QuickRecon/DiveCANHead/Firmware/BENCHTEST.md

# DiveCAN Jr Hardware-in-the-Loop Test Checklist

Manual hardware bench tests required before merging changes to the
OTA, power, or boot subsystems. Each entry is structured so it can be
lifted into the `tests/integration/` pytest harness later —
preconditions, actions, and pass criteria are expressed in concrete,
scriptable terms.

The existing integration harness (Arduino Due cell-shim, Riden PSU
control, CAN dongle) supplies most of the plumbing needed to automate
each entry. Until that automation exists, these are run by hand
during phase merges and the results recorded in the PR description.

**Maintenance directive:** when adding or modifying a safety-critical
behaviour, add or update the corresponding entry here in the same PR.
Same convention as `ARCHITECTURE.md` and `COMPROMISE.md`.

---

## Section 1 — Boot & power (Phase 1)

### BT-1.1 Cold-boot from clean flash

- **Pre:** Unit freshly programmed via `flash.sh` (MCUBoot + signed
  app via sysbuild merged hex). External NOR fully erased
  (`flash_erase 0 64M` on the SPI NOR via probe).
- **Action:** Power on. Observe heartbeat LED and RTT log.
- **Pass:**
  - MCUBoot startup messages on RTT within 1 s.
  - Heartbeat LED blinks during MCUBoot's pre-boot window
    (driven by `CONFIG_MCUBOOT_INDICATION_LED`).
  - App reaches its main loop within 3 s of power-on.
  - App's heartbeat thread takes over the LED.
  - No errors in MCUBoot output relating to slot1/scratch
    (acceptable: "no image in secondary slot" — slot is empty).

### BT-1.2 Settings persistence across reboot

- **Pre:** BT-1.1 passed. Unit is running normally.
- **Action:**
  1. Write a known runtime setting via UDS (e.g. PPO2 control mode
     to a non-default value).
  2. Power-cycle.
  3. Read the setting back via UDS.
- **Pass:** The setting matches what was written. Confirms NVS
  storage on external NOR is functional.

### BT-1.3 Mid-erase power pull on external NOR

- **Pre:** Begin a `flash_erase` operation on the slot1 partition
  (192–224 KB region). Pull power at ~50 % of the erase.
- **Action:** Restore power. Observe boot.
- **Pass:**
  - Unit boots from slot0 (running app).
  - No MCUBoot stall — partial-erased slot1 may report "no image"
    or "invalid header" in RTT, both acceptable.
  - App reaches main loop.
  - No persistent fault state in error histogram (0xF260).

### BT-1.4 IWDG survival across MCUBoot startup

- **Pre:** Soft-reset the unit via `sys_reboot()` (e.g. from a UDS
  command in a confirmed image).
- **Action:** Observe boot.
- **Pass:**
  - IWDG (8 s window) does NOT trip during MCUBoot's hash walk +
    swap-state read.
  - App reaches its main loop within the same ~3 s budget as
    BT-1.1.
  - Implicit confirmation of `CONFIG_BOOT_WATCHDOG_FEED=y` working.

### BT-1.5 Heartbeat-LED handoff

- **Pre:** Unit running normally for ≥30 s.
- **Action:** Visually inspect heartbeat LED behaviour across a
  power cycle.
- **Pass:**
  - During MCUBoot window: LED blinks at MCUBoot's
    indication-LED cadence (typically faster than the app's
    heartbeat).
  - After app boot: LED blinks at the app's heartbeat cadence.
  - Smooth handoff, no extended dark period.

### BT-1.6 Signed slot0 image validates on every boot (Phase 2)

- **Pre:** Unit programmed via `flash.sh` (sysbuild merged hex
  containing MCUBoot + an imgtool-signed v0.0.0+0 app). MCUBoot
  Kconfig has `CONFIG_BOOT_VALIDATE_SLOT0=y` (verify via
  `grep BOOT_VALIDATE build/mcuboot/zephyr/.config`).
- **Action:** Cold power-cycle and observe RTT log up to the app
  banner.
- **Pass:**
  - MCUBoot logs a successful slot0 validation pass (no
    `Image in the primary slot is not valid!` line).
  - App banner `DiveCAN Jr — Zephyr <version>` appears.
  - SHA-256 walk completes in well under the 8 s IWDG window —
    confirms `BOOT_WATCHDOG_FEED=y` is alive during the hash.
- **Notes:** Image layout reference (from `scripts/sign_app.py`
  output): 512 B header + body + 40 B TLV (single SHA-256 entry,
  TLV type 0x10). `python3 imgtool.py verify` against the
  signed bin should print `Image was correctly validated`.

### BT-1.7 Corrupt byte in slot0 → MCUBoot refuses to jump (Phase 2)

- **Pre:** Unit running normally from a known-good signed image.
  External NOR / slot1 state irrelevant.
- **Action:** Run `scripts/test_mcuboot_reject.sh`. The script:
  1. Copies the freshly-built `zephyr.signed.bin`, flips one byte
     at offset 0x1000 (past the 512 B header, before the TLV).
  2. Reflashes only slot0 at `0x08010000` via STM32CubeProgrammer —
     MCUBoot itself is untouched.
  3. Halts the chip via openocd, reads PC, dumps the SEGGER RTT
     up-buffer in RAM (`pBuffer`, `WrOff` from the control block).
  4. Prints the captured MCUBoot log + PASS/FAIL verdict.
- **Pass:**
  - Script prints **`PASS: MCUBoot rejected the corrupt image`**.
  - PC at halt is inside MCUBoot text (`< 0x08010000`).
  - When MCUBoot reaches its FIH_PANIC log path, the RTT buffer
    contains the textbook chain:
    `Image in the primary slot is not valid!` → `Unable to find
    bootable image`. (On the early-validation path the chip
    panics through `arch_system_halt` before that log line gets
    a chance — the PC check is still the authoritative verdict.)
  - Heartbeat LED does **not** transition to the app's cadence.
- **Recovery:** `./flash.sh` (the script prints this on exit too).
- **Notes:**
  - We dump the RTT up-buffer directly from RAM via openocd's
    `mdb` rather than running the live `rtt server` bridge.
    MCUBoot's writes happen in tens of ms during early boot and
    are long over by the time openocd's RTT poll thread finds
    the control block. The buffer-dump method is deterministic
    and avoids the host-attach race.
  - This is the most important defensive property of the
    bootloader and must remain green after any MCUBoot config
    change.
  - The pre-existing `E: Watchdog install timeout failed: -22`
    line in MCUBoot's output is unrelated — it fires whenever
    the L4 IWDG is already running from a prior boot, which is
    expected on warm-reset and harmless here (`BOOT_WATCHDOG_FEED`
    keeps the running IWDG fed regardless).

---

## Section 2 — OTA transfer (Phase 3)

The wire-protocol behaviour for SIDs 0x10 / 0x34 / 0x36 / 0x37 / 0x31 is
covered automatically by:

- **`tests/uds_ota/`** — native_sim ztest suite, 25 cases (run with
  `scripts/native_test.py run uds_ota`)
- **`tests/integration/harness/test_uds_ota.py`** — pytest E2E suite,
  8 cases over vcan against the real Zephyr firmware (run with
  `pytest test_uds_ota.py` from the harness venv)

The bench tests below catch what the host harness can't: the real
MCUBoot bootloader doing the actual swap on STM32L4 silicon. Until the
"Enable MCUBoot E2E on native_sim" follow-up lands, this section is the
authoritative coverage for the swap path.

### BT-2.1 Happy path: streamed image swaps in

- **Pre:** Unit running a confirmed v1 image. SD card / external NOR in
  whatever state — slot1 contents irrelevant.
- **Action:**
  1. Use the existing `tests/integration/harness/uds_ota.py` helpers (or
     equivalent dive-computer tool) over a USB CAN adapter:
     ```
     ota.enter_programming()
     ota.request_download(len(image))
     ota.transfer_image(image)
     ota.request_transfer_exit()
     ota.routine_activate()
     ```
  2. Wait ~15 s for MCUBoot's swap-using-scratch to complete.
  3. Power-cycle (or watch the reboot fire from the activate response).
- **Pass:**
  - Each UDS request gets a positive response (0x50 / 0x74 / 0x76 / 0x77
    / 0x71).
  - On the next boot, the running firmware is v2 (query DID 0xF000 to
    confirm).
  - No `Image in the primary slot is not valid!` line in MCUBoot's RTT
    log.
  - **The unit is now booting from a test-mode image — Phase 4 POST
    confirmation hasn't landed yet, so the image will revert on the
    next reboot unless `boot_write_img_confirmed()` is called manually
    via SWD.** This is the documented Phase 3 → Phase 4 gap; flagged in
    the OTA plan.

### BT-2.2 Header rejection at 0x37

- **Pre:** Unit running a confirmed image.
- **Action:** Run `tests/integration/harness/test_uds_ota.py`'s
  `truncate_image_header()` helper to zero the MCUBoot magic, then
  stream that corrupted image via 0x34 / 0x36 / 0x37.
- **Pass:**
  - 0x37 returns NRC (0x22 or 0x72).
  - slot0 is **untouched** — `mcuboot_swap_type()` reports
    BOOT_SWAP_TYPE_NONE on next read.
  - `boot_request_upgrade` was never called.

### BT-2.3 Hash rejection at 0x31 activate

- **Pre:** Unit running a confirmed image.
- **Action:** Use `corrupt_signed_image()` to flip a byte inside the
  body of a valid signed image. Stream the full 0x34/0x36/0x37/0x31
  sequence.
- **Pass:**
  - 0x37 succeeds (header magic + size still valid).
  - 0x31 returns NRC 0x22 (CONDITIONS_NOT_CORRECT) — the firmware-side
    SHA-256 walk caught the corruption before the bootloader was
    invoked.
  - `boot_request_upgrade` was never called.
  - The unit stays alive, no reboot.

### BT-2.4 Programming session refused mid-dive

- **Pre:** Unit running a confirmed image. Pressure transducer
  registering surface (~1013 mbar).
- **Action:**
  1. Pressurise the depth chamber (or inject a high `chan_atmos_pressure`
     via the test rig) to simulate descent past 2 m → ambient > 1200 mbar.
  2. From the host: send `SID 0x10 subfunction 0x02` (enter programming
     session).
- **Pass:**
  - DUT replies NRC 0x22 — programming session denied.
  - Surface, pressure back to ~1013 mbar.
  - Retry session control: positive response, session enters
    programming.
  - Confirms the safety property "no flash operations underwater" holds
    across the depth threshold.

## Section 3 — POST + confirm (Phase 4)

The state-machine wire behaviour (each per-check pass/fail path,
overall-deadline expiry, pass-mask transitions) is covered by:

- **`tests/firmware_confirm/`** — native_sim ztest suite, 13 cases
  (run with `scripts/native_test.py run firmware_confirm`).

The bench tests below catch what the host harness can't: an actual
warm reboot path, the MCUBoot revert handshake on the next boot, and
the real IWDG ticking through the 45 s window. Real hardware is the
authoritative coverage for the rollback property; the host suite is
the authoritative coverage for the state machine.

### BT-3.1 Happy path: handset present, image auto-confirms

- **Pre:** Slot1 has a known-good signed v2 image streamed via
  BT-2.1; unit booted and is running the v2 image but it has NOT been
  manually confirmed (DID 0xF270 byte 1 reports `confirmed=0` on
  cold-boot to v2). Pressure transducer at surface (~1013 mbar).
  Handset plugged in and exchanging BUS_INIT / BUS_ID with the unit.
- **Action:** Power-cycle. Wait up to 45 s.
- **Pass:**
  - RTT log shows `<inf> fw_confirm: POST passed — image confirmed`
    within 5–10 s.
  - DID 0xF270 byte 1 returns 1 (`confirmed`).
  - DID 0xF271 (POST state) returns ::POST_CONFIRMED (`0x06`).
  - Heartbeat LED keeps blinking at the app's normal cadence — no
    reboot.
  - Subsequent power-cycle still boots v2 (the confirm sticks).

### BT-3.2 No handset → rollback

- **Pre:** Same as BT-3.1 but **leave the handset disconnected**.
- **Action:** Power-cycle. Wait up to 60 s.
- **Pass:**
  - RTT log shows `<err> fw_confirm: POST failed in state 11 — rebooting`
    (state 11 = ::POST_FAILED_NO_HANDSET) within 45 s of cold boot.
  - Unit reboots; MCUBoot's RTT output on the next boot reports a
    revert-using-scratch operation.
  - After the swap completes, DID 0xF272 (running version) reports the
    previous (v1) image, not v2.
  - Error histogram (DID 0xF260) shows OP_ERR_POST_FAIL (code 33)
    incremented by one.

### BT-3.3 Cell failure mid-POST → rollback

- **Pre:** Slot1 has a known-good v2 image, ready to confirm.
- **Action:**
  1. Physically disconnect one analog cell (or hold its DAC line at
     0 V on the test rig so the cell driver publishes CELL_FAIL).
  2. Power-cycle.
- **Pass:**
  - POST fails in state 8 (::POST_FAILED_CELL) within the 10 s cell
    sub-timeout.
  - Unit reboots; MCUBoot reverts.
  - Error histogram bumps OP_ERR_POST_FAIL with detail=8.
  - Reconnect the cell, power-cycle: v1 boots and POST is silent
    (image already confirmed).

### BT-3.4 Consensus failure → rollback

- **Pre:** Slot1 has a v2 image. Cells healthy individually but
  consensus deliberately broken (e.g. cells reporting widely disagreeing
  PPO2 values past `MAX_DEVIATION`, so `consensus_ppo2` stays
  `PPO2_FAIL`).
- **Action:** Power-cycle.
- **Pass:**
  - POST fails in state 9 (::POST_FAILED_CONSENSUS) within the 5 s
    consensus sub-timeout.
  - Unit reboots; MCUBoot reverts to v1.
  - Histogram OP_ERR_POST_FAIL detail=9.

### BT-3.5 No PPO2 broadcast → rollback

- **Pre:** Slot1 has v2 with the periodic broadcaster intentionally
  disabled (e.g. a debug build where `divecan_ppo2_tx` is commented out
  or a Kconfig that omits it).
- **Action:** Power-cycle.
- **Pass:**
  - POST fails in state 10 (::POST_FAILED_NO_PPO2_TX) within 5 s.
  - MCUBoot reverts to v1.
  - Histogram OP_ERR_POST_FAIL detail=10.

### BT-3.6 Solenoid stuck → rollback

- **Pre:** Slot1 has v2. Solenoid sensing wired to report
  `DIVECAN_ERR_SOL_UNDERCURRENT` or `OVERCURRENT` (e.g. cut wire,
  shorted return). Only meaningful on variants with
  `CONFIG_HAS_O2_SOLENOID=y`.
- **Action:** Power-cycle. Wait up to 60 s.
- **Pass:**
  - POST fails in state 12 (::POST_FAILED_SOLENOID) within the 2 s
    solenoid sub-timeout (after cells + consensus + TX + handset have
    already passed).
  - MCUBoot reverts.
  - Histogram OP_ERR_POST_FAIL detail=12.

### BT-3.7 Overall deadline expiry (slow boot scenario)

- **Pre:** Slot1 has v2. Choose a stress configuration where every
  individual sub-check would eventually pass but cumulatively exceeds
  45 s — e.g. three DiveO2 cells, all with their startup latency
  artificially extended (cold sensors).
- **Action:** Power-cycle, monitor RTT.
- **Pass:**
  - POST fails in state 7 (::POST_FAILED_TIMEOUT) at 45 s ± 1 s.
  - MCUBoot reverts on the next boot.
  - Histogram OP_ERR_POST_FAIL detail=7.

### BT-3.8 Confirmed image: POST is silent on subsequent boots

- **Pre:** v2 confirmed via BT-3.1. Cold-boot the unit several times.
- **Action:** Observe RTT on each boot.
- **Pass:**
  - RTT shows `<inf> fw_confirm: Image already confirmed — POST silent`
    in lieu of the full POST sequence.
  - Heartbeat takes over the LED inside ~3 s (same budget as BT-1.1).
  - No `boot_write_img_confirmed` retry call appears on the log.

## Section 4 — Factory backup (Phase 5)

The capture and restore logic, the verify-after-write step, the
idempotency guarantee, the mid-write fault path, and the version
reader are all covered by:

- **`tests/factory_image/`** — native_sim ztest suite, 15 cases
  (run with `scripts/native_test.py run factory_image`).

The bench tests below catch what the host harness can't: actual SPI
NOR write/erase timing, the watchdog cooperation during the multi-
second copy, and the persistence of the captured flag across a real
power cycle.

### BT-4.1 First-boot capture from factory-fresh hardware

- **Pre:** Unit freshly programmed via `flash.sh` from a clean state
  (`flash_erase 0 64M` on the SPI NOR via probe, so any prior
  `factory/captured` NVS key is gone). MCUBoot + signed slot0 image
  flashed via the merged hex. Power-cycle to land on a confirmed boot.
- **Action:** Power on and wait up to 30 s.
- **Pass:**
  - RTT log shows `<inf> factory_image: Factory image captured`.
  - DID 0xF270 byte 3 bit 0 transitions from 0 → 1 within 30 s.
  - Reading the factory partition over SWD shows the same bytes as
    slot0's signed image.
  - DID 0xF274 (factory version) returns the same payload as DID
    0xF272 (running version).

### BT-4.2 Capture survives across power cycle

- **Pre:** BT-4.1 passed; unit running normally, factory captured.
- **Action:** Power-cycle ≥3 times.
- **Pass:**
  - Each boot shows `<inf> factory_image: Factory image already
    captured — capture_work is a no-op` (or omits the line entirely
    because the work is a fast no-op).
  - DID 0xF270 byte 3 bit 0 remains 1.
  - Factory partition contents unchanged between power cycles
    (verify via SWD readback hash).
  - No SPI NOR writes occur after boot (probe the SPI bus, or check
    that the OP_ERR_FLASH counter in DID 0xF260 doesn't bump).

### BT-4.3 Mid-capture power pull

- **Pre:** BT-4.1 not yet run (NVS captured flag absent). Wire the
  Riden PSU control to cut power 5 s after boot — long enough for
  capture to be well underway but not far enough for the
  verify-and-mark step to complete.
- **Action:** Power on, observe RTT, then PSU pulls power at T+5s.
  Restore power.
- **Pass:**
  - On the next boot, RTT shows the capture re-attempting from
    scratch — `factory/captured` was never written, so the engine
    treats the partial partition as garbage and erases it.
  - Eventually capture succeeds; DID 0xF270 flips its captured bit.
  - The error histogram (DID 0xF260) shows OP_ERR_FLASH bumped at
    least once (the first attempt's incomplete write triggered no
    error — but the second attempt's erase fires under nominal
    conditions, no error expected there).

### BT-4.4 Restore-from-factory via UDS

- **Pre:** Factory captured (BT-4.1). OTA a different v2 image and
  confirm it (BT-3.1) so the running slot0 differs from the factory
  copy.
- **Action:** Send UDS write to DID 0xF276 with payload `0x01`.
- **Pass:**
  - DUT replies positively to the write.
  - RTT shows `<inf> factory_image: Factory image staged for swap —
    rebooting` after ~2 s of SPI NOR activity.
  - Unit reboots; MCUBoot swaps slot1 (factory copy) into slot0.
  - On next boot, DID 0xF272 (running version) matches the original
    factory version (back to v1, not v2).
  - DID 0xF270 captured bit still 1 — restore doesn't clear the
    factory backup.
  - POST runs and confirms (the factory image trivially passes).

### BT-4.5 Force re-capture (UDS DID 0xF277)

- **Pre:** Factory v1 captured. OTA + confirm to v2.
- **Action:** Send UDS write to DID 0xF277 with payload `0x01`.
- **Pass:**
  - DUT replies positively.
  - Within 30 s, RTT shows `<inf> factory_image: Factory image
    re-captured (forced)`.
  - DID 0xF274 (factory version) now matches the v2 running version.
  - DID 0xF270 captured bit remains 1 throughout.
  - SPI NOR readback confirms the factory partition now contains
    v2 bytes.

### BT-4.6 Restore refused if no factory captured

- **Pre:** Fresh-flashed unit, BT-4.1 not yet run, factory partition
  effectively garbage.
- **Action:** Send UDS write to DID 0xF276 with payload `0x01`.
- **Pass:**
  - DUT replies with NRC 0x22 (CONDITIONS_NOT_CORRECT).
  - No SPI NOR activity; no reboot.
  - Slot1 unchanged.

### BT-4.7 Long capture doesn't trip IWDG

- **Pre:** BT-4.1 about to run (capture imminent).
- **Action:** Power on and watch the heartbeat LED + RTT throughout
  the capture window.
- **Pass:**
  - Heartbeat LED keeps blinking through the entire ~20 s capture
    (no IWDG reset, no missed feed log line from watchdog_feeder).
  - `heartbeat_set_long_op(true/false)` bracketing the capture
    suppresses the per-slot liveness check inside that window —
    no `Heartbeat slot N stalled` WRN lines in RTT during capture.
  - Once capture completes, normal heartbeat behaviour resumes.

## Section 5 — UDS OTA diagnostics (Phase 6)

Phase 6 surfaces full MCUBoot / OTA / factory state through the UDS
DID namespace at 0xF27x. The wire dispatch + session/dive gating +
magic-byte checks are covered by:

- **`tests/uds_state_did_ota/`** — native_sim ztest suite, 31 cases
  (run with `scripts/native_test.py run uds_state_did_ota`).
- **`tests/integration/harness/test_uds_did_ota.py`** — pytest
  integration cases run against a running firmware on the test stand.

The bench tests below verify the diagnostics behave correctly against
real MCUBoot state — pre/post swap, pre/post factory capture, pre/post
POST confirmation — which the native_sim harness cannot fake because
the bootloader doesn't run there.

### BT-5.1 MCUBOOT_STATUS reflects a clean confirmed boot

- **Pre:** Freshly flashed unit, BT-1.1 passed (cold boot to confirmed
  state, factory captured).
- **Action:** Read DID 0xF270.
- **Pass:**
  - Payload is exactly 16 bytes.
  - Byte 0 (swap_type) = 0 (BOOT_SWAP_TYPE_NONE).
  - Byte 1 (confirmed) = 1.
  - Byte 2 (running slot) = 0.
  - Byte 3 bit 0 (factory captured) = 1.
  - Bytes 4–7 (slot0 truncated sem_ver) match `git describe` of the
    flashed image.
  - Bytes 8–11 (slot1 truncated sem_ver) = 0xFF×4 (no staged OTA).
  - Bytes 12–15 (factory truncated sem_ver) match bytes 4–7
    (factory was captured from this slot0).

### BT-5.2 MCUBOOT_STATUS during a staged OTA

- **Pre:** BT-5.1 passed. OTA a different v2 image up to slot1 via
  the 0x34/0x36/0x37 pipeline but **do not** activate (skip 0x31).
- **Action:** Read DID 0xF270 then DID 0xF273.
- **Pass:**
  - 0xF270 byte 1 (confirmed) = 1 (running image still confirmed).
  - 0xF270 bytes 8–11 now contain v2's truncated sem_ver (not 0xFF×4).
  - 0xF273 returns v2's full 8-byte sem_ver including build_num.
  - 0xF272 still returns the running v1 sem_ver.

### BT-5.3 MCUBOOT_STATUS after activation, before confirm

- **Pre:** BT-5.2 staged. Activate via SID 0x31 RID 0xF001. Reboot
  happens; new image boots; POST runs but is not yet complete.
- **Action:** During POST (before confirmation), read DID 0xF270.
- **Pass:**
  - Byte 0 (swap_type) reports the MCUBoot post-swap state — typically
    0 (NONE) by the time the app is running, because the swap has
    already been committed.
  - Byte 1 (confirmed) = 0 until POST completes, 1 after.
  - 0xF271 byte 0 transitions through POST_WAITING_* states then
    reaches POST_CONFIRMED.

### BT-5.4 POST_STATUS pass-mask accumulates checks

- **Pre:** Fresh boot with a known-working v2 image awaiting confirm.
- **Action:** Poll DID 0xF271 at 1 Hz for the duration of POST
  (~5–10 s depending on cell type).
- **Pass:**
  - Byte 1 (pass_mask) starts at 0 and accumulates bits:
    `POST_PASS_BIT_CELLS` then `_CONSENSUS` then `_PPO2_TX` then
    `_HANDSET` (and `_SOLENOID` on solenoid variants).
  - On reaching the all-ones mask, byte 0 transitions to
    POST_CONFIRMED.
  - Reserved bytes 2 and 3 stay 0 throughout.

### BT-5.5 OTA_VERSION matches git describe at flash time

- **Pre:** Unit flashed with a known git ref.
- **Action:** Read DID 0xF272.
- **Pass:**
  - Returned 8 bytes match the imgtool-signed image version field
    (major / minor / revision_le16 / build_num_le32).
  - Cross-check by reading slot0 header directly via SWD at offset
    20 — the bytes must be byte-identical.

### BT-5.6 OTA_PENDING_VERSION reports 0xFF×8 when slot1 is empty

- **Pre:** Fresh unit, no OTA staged, slot1 either un-touched or
  explicitly erased via probe.
- **Action:** Read DID 0xF273.
- **Pass:**
  - Payload is exactly 8 bytes of 0xFF.

### BT-5.7 OTA_FACTORY_VERSION reports captured version

- **Pre:** BT-4.1 passed (factory captured at v1).
- **Action:** Read DID 0xF274.
- **Pass:**
  - 8-byte payload matches the slot0 sem_ver at the time of capture
    (i.e. v1's sem_ver), and matches what 0xF272 returned right
    before the first OTA.
  - After OTA to v2 + confirm, 0xF274 still returns v1's sem_ver
    (factory backup is sticky across OTAs).

### BT-5.8 Force-revert via DID 0xF275 returns previous image

- **Pre:** Fresh unit confirmed at v1. OTA to v2 + confirm
  (slot1 now holds v1 from the swap). Read DID 0xF272 — confirms v2
  running.
- **Action:** Enter programming session (SID 0x10 subfunction 0x02).
  Send UDS write to DID 0xF275 with payload `0x01`.
- **Pass:**
  - DUT replies positively to the write.
  - Unit reboots within ~250 ms.
  - On next boot, DID 0xF272 returns v1 (rollback succeeded).
  - DID 0xF273 now holds v2 (the swap put v2 back into slot1).
  - POST passes within the deadline (v1 already proven good).

### BT-5.9 Write DIDs refused outside programming session

- **Pre:** Fresh boot, no diagnostic session entered.
- **Action:** For each of 0xF275 / 0xF276 / 0xF277, send a WDBI
  write with payload `0x01`.
- **Pass:**
  - Each request gets a UDS negative response with NRC 0x7F
    (SERVICE_NOT_IN_SESSION).
  - No reboot, no SPI NOR activity, no factory partition writes.

### BT-5.10 Write DIDs refused during a dive

- **Pre:** Programming session entered. Use the integration test
  harness to inject `chan_atmos_pressure = 2000` (~10 m head).
- **Action:** Send WDBI to any of 0xF275 / 0xF276 / 0xF277 with
  payload `0x01`.
- **Pass:**
  - First request: session is force-downgraded to DEFAULT by
    `UDS_MaintainSession` and the handler refuses with NRC 0x7F
    (SERVICE_NOT_IN_SESSION).
  - RTT shows `<wrn> uds: Dive detected: programming session
    forced -> default`.
  - Subsequent re-entry attempts at SID 0x10 0x02 also refused
    (NRC 0x22 from the dive check in the session-control handler).

### BT-5.11 Write DIDs reject wrong magic byte

- **Pre:** Programming session entered, surface ambient pressure.
- **Action:** Send WDBI to 0xF275 with payload `0xFF` (or any
  byte ≠ 0x01).
- **Pass:**
  - NRC 0x31 (REQUEST_OUT_OF_RANGE).
  - No reboot, no SPI NOR activity.
  - Subsequent write with payload `0x01` succeeds — the wrong-byte
    rejection doesn't latch the channel into a refused state.

### BT-5.12 Force-revert refused with empty slot1

- **Pre:** Fresh confirmed unit, slot1 erased (probe-driven
  `flash_erase` on slot1's partition range).
- **Action:** Enter programming session. Send WDBI to 0xF275 with
  payload `0x01`.
- **Pass:**
  - NRC 0x22 (CONDITIONS_NOT_CORRECT).
  - RTT shows `<wrn> uds: Force-revert refused: slot1 header read
    failed -ENOENT`.
  - No reboot.

### BT-5.13 Restore-factory refused with no captured backup

- **Pre:** Fresh-flashed unit, `factory/captured` NVS key not set
  yet (capture hasn't run, or NVS was wiped).
- **Action:** Enter programming session. Send WDBI to 0xF276 with
  payload `0x01`.
- **Pass:**
  - NRC 0x22 (CONDITIONS_NOT_CORRECT).
  - RTT shows `<wrn> uds: Restore-factory refused: no captured
    factory image`.
  - No reboot, no SPI NOR activity.

### BT-5.14 Force-capture refused with unconfirmed image

- **Pre:** Stage an OTA + activate but do NOT let POST confirm
  (e.g. simulate a POST failure via the integration shim by holding
  PPO2_TX counter at 0). Image is running in test mode,
  `boot_is_img_confirmed()` returns false.
- **Action:** Enter programming session. Send WDBI to 0xF277 with
  payload `0x01`.
- **Pass:**
  - NRC 0x22 (CONDITIONS_NOT_CORRECT).
  - RTT shows `<wrn> uds: Force-capture refused: running image is
    not confirmed`.
  - Factory partition unchanged.

### BT-5.15 Force-capture overwrites the factory backup

- **Pre:** Factory at v1 (BT-4.1). OTA + confirm to v2. DID 0xF274
  still reports v1.
- **Action:** Enter programming session. Send WDBI to 0xF277 with
  payload `0x01`.
- **Pass:**
  - DUT replies positively immediately (capture runs asynchronously
    on the factory work queue).
  - Within ~20 s, RTT shows `<inf> factory_image: Factory image
    re-captured (forced)`.
  - DID 0xF274 now returns v2's sem_ver.
  - DID 0xF270 captured bit stays 1 throughout.

## Section 6 — Backport (Phase 7, separate ticket)

_SD-card-equipped older hardware: full OTA cycle via the
flash-disk-wrapper driver, SD-removal-during-OTA fault injection,
FAT corruption recovery._
