QuickRecon/DiveCANHead/Firmware/reports/rom_report.txt

-- west build: running target rom_report
[0/1] cd /home/aren/Nextcloud/Clients/Internal/CCR_Electronics/DiveCANHeadRev2/Firmware/build && /home/aren/ncs/toolchains/927563c840/usr/local/bin/python3.12 /home/aren/Nextcloud/Clients/Internal/CCR_Electronics/DiveCANHeadRev2/zephyr/scripts/footprint/size_report -k /home/aren/Nextcloud/Clients/Internal/CCR_Electronics/DiveCANHeadRev2/Firmware/build/zephyr/zephyr.elf -z /home/aren/Nextcloud/Clients/Internal/CCR_Electronics/DiveCANHeadRev2/zephyr -o /home/aren/Nextcloud/Clients/Internal/CCR_Electronics/DiveCANHeadRev2/Firmware/build --workspace=/home/aren/Nextcloud/Clients/Internal/CCR_Electronics/DiveCANHeadRev2 -d 99 --json rom.json rom
Path                                                                                             Size       %  Address    Section    
==========================================================================================================================================
Root                                                                                           182770 100.00%  - 
├── (hidden)                                                                                    22762  12.45%  - 
├── (no paths)                                                                                  11910   6.52%  - 
│   ├── CSWTCH.1                                                                                   16   0.01%  0x08034fb4 rodata
│   ├── CSWTCH.1015                                                                                 5   0.00%  0x0803b725 rodata
│   ├── CSWTCH.2085                                                                                12   0.01%  0x08035968 rodata
│   ├── CSWTCH.21                                                                                  17   0.01%  0x0803b811 rodata
│   ├── CSWTCH.3162                                                                                 6   0.00%  0x08035b64 rodata
│   ├── CSWTCH.4939                                                                                 7   0.00%  0x0803b71e rodata
│   ├── CSWTCH.497                                                                                 20   0.01%  0x0803597c rodata
│   ├── CSWTCH.552                                                                                 12   0.01%  0x08034f78 rodata
│   ├── DOUBLE_POW5_INV_SPLIT2                                                                    240   0.13%  0x08034e40 rodata
│   ├── DOUBLE_POW5_SPLIT2                                                                        208   0.11%  0x08034d70 rodata
│   ├── DOUBLE_POW5_TABLE                                                                         208   0.11%  0x08034ca0 rodata
│   ├── POW5_INV_OFFSETS                                                                           88   0.05%  0x08035b0c rodata
│   ├── POW5_OFFSETS                                                                               84   0.05%  0x08035ab8 rodata
│   ├── __adddf3                                                                                  630   0.34%  0x08010395 text
│   ├── __addsf3                                                                                  352   0.19%  0x08010d9d text
│   ├── __aeabi_cdcmple                                                                            16   0.01%  0x08010bc1 text
│   ├── __aeabi_cdrcmple                                                                           32   0.02%  0x08010bb1 text
│   ├── __aeabi_cfcmpeq                                                                            16   0.01%  0x080112c5 text
│   ├── __aeabi_cfrcmple                                                                           24   0.01%  0x080112bd text
│   ├── __aeabi_d2f                                                                               158   0.09%  0x08010cf1 text
│   ├── __aeabi_d2uiz                                                                              64   0.04%  0x08010cb1 text
│   ├── __aeabi_dcmpeq                                                                             18   0.01%  0x08010bd1 text
│   ├── __aeabi_dcmpge                                                                             18   0.01%  0x08010c0d text
│   ├── __aeabi_dcmpgt                                                                             18   0.01%  0x08010c21 text
│   ├── __aeabi_dcmple                                                                             18   0.01%  0x08010bf9 text
│   ├── __aeabi_dcmplt                                                                             18   0.01%  0x08010be5 text
│   ├── __aeabi_dcmpun                                                                             44   0.02%  0x08010c35 text
│   ├── __aeabi_ddiv                                                                              464   0.25%  0x08010955 text
│   ├── __aeabi_dmul                                                                              596   0.33%  0x08010701 text
│   ├── __aeabi_dsub                                                                              634   0.35%  0x08010391 text
│   ├── __aeabi_f2d                                                                                66   0.04%  0x08010651 text
│   ├── __aeabi_f2iz                                                                               76   0.04%  0x08011339 text
│   ├── __aeabi_f2uiz                                                                              62   0.03%  0x08011385 text
│   ├── __aeabi_fcmpeq                                                                             18   0.01%  0x080112d5 text
│   ├── __aeabi_fcmpge                                                                             18   0.01%  0x08011311 text
│   ├── __aeabi_fcmpgt                                                                             18   0.01%  0x08011325 text
│   ├── __aeabi_fcmple                                                                             18   0.01%  0x080112fd text
│   ├── __aeabi_fcmplt                                                                             18   0.01%  0x080112e9 text
│   ├── __aeabi_frsub                                                                             364   0.20%  0x08010d91 text
│   ├── __aeabi_fsub                                                                              356   0.19%  0x08010d99 text
│   ├── __aeabi_i2d                                                                                34   0.02%  0x0801062d text
│   ├── __aeabi_ldiv0                                                                               2   0.00%  0x080114d1 text
│   ├── __aeabi_memcpy4                                                                            28   0.02%  0x080336a1 text
│   ├── __aeabi_ui2f                                                                               36   0.02%  0x08010efd text
│   ├── __aeabi_ul2d                                                                              106   0.06%  0x08010695 text
│   ├── __atof_engine                                                                             268   0.15%  0x08033821 text
│   ├── __ceil_log2pow5                                                                            16   0.01%  0x0802f4a5 text
│   ├── __cmpdf2                                                                                  122   0.07%  0x08010b35 text
│   ├── __compound_literal.0                                                                        8   0.00%  0x080358bc rodata
│   ├── __divsf3                                                                                  310   0.17%  0x08011115 text
│   ├── __double_computeInvPow5                                                                   248   0.14%  0x0802f59d text
│   ├── __double_computePow5                                                                      232   0.13%  0x0802f4b5 text
│   ├── __file_str_put                                                                             16   0.01%  0x08033a1d text
│   ├── __fixdfsi                                                                                  78   0.04%  0x08010c61 text
│   ├── __fixunsdfdi                                                                               60   0.03%  0x08011495 text
│   ├── __floatdidf                                                                                90   0.05%  0x080106a5 text
│   ├── __floatdisf                                                                               124   0.07%  0x08010f31 text
│   ├── __floatsisf                                                                                28   0.02%  0x08010f05 text
│   ├── __floatundisf                                                                             140   0.08%  0x08010f21 text
│   ├── __floatunsidf                                                                              30   0.02%  0x0801060d text
│   ├── __fpclassifyf                                                                              52   0.03%  0x0802f779 text
│   ├── __func__.0                                                                                 14   0.01%  0x0803b75d rodata
│   ├── __func__.0                                                                                 18   0.01%  0x0803b7c5 rodata
│   ├── __gedf2                                                                                   138   0.08%  0x08010b25 text
│   ├── __gtsf2                                                                                   110   0.06%  0x0801124d text
│   ├── __i_vfprintf                                                                             1138   0.62%  0x0802f025 text
│   ├── __isnanf                                                                                   16   0.01%  0x08033a0d text
│   ├── __ledf2                                                                                   130   0.07%  0x08010b2d text
│   ├── __log2pow5                                                                                 12   0.01%  0x0802f499 text
│   ├── __ltsf2                                                                                   102   0.06%  0x08011255 text
│   ├── __memcpy_chk                                                                               38   0.02%  0x080336cd text
│   ├── __mulPow5InvDivPow2                                                                        38   0.02%  0x0803395b text
│   ├── __mulPow5divPow2                                                                           32   0.02%  0x08033981 text
│   ├── __mulsf3                                                                                  360   0.20%  0x08010fad text
│   ├── __nesf2                                                                                    94   0.05%  0x0801125d text
│   ├── __popcountsi2                                                                              38   0.02%  0x080114f9 text
│   ├── __pow5bits                                                                                 16   0.01%  0x0802f7ad text
│   ├── __shiftright128                                                                            62   0.03%  0x080339cf text
│   ├── __strtok_r                                                                                 80   0.04%  0x08033797 text
│   ├── __udivmoddi4                                                                              700   0.38%  0x0801151f text
│   ├── __ultoa_invert                                                                             52   0.03%  0x080337ed text
│   ├── __umul128                                                                                  46   0.03%  0x080339a1 text
│   ├── cal_failed_entry                                                                           12   0.01%  0x0802f821 text
│   ├── lround                                                                                    156   0.09%  0x0802f6dd text
│   ├── memcmp                                                                                     32   0.02%  0x080336f3 text
│   ├── memset                                                                                     16   0.01%  0x080336bd text
│   ├── mulShift32                                                                                 46   0.03%  0x0803392d text
│   ├── pstr_an                                                                                     3   0.00%  0x0803b825 rodata
│   ├── pstr_nfinity                                                                                8   0.00%  0x0803b828 rodata
│   ├── roundf                                                                                     72   0.04%  0x0802f695 text
│   ├── snprintf                                                                                   84   0.05%  0x0802ebf5 text
│   ├── strcmp                                                                                     20   0.01%  0x080114d5 text
│   ├── strcspn                                                                                    34   0.02%  0x08033713 text
│   ├── strlen                                                                                     16   0.01%  0x080114e9 text
│   ├── strncmp                                                                                    36   0.02%  0x08033735 text
│   ├── strncpy                                                                                    38   0.02%  0x08033759 text
│   ├── strnlen                                                                                    24   0.01%  0x0803377f text
│   ├── strtof                                                                                    756   0.41%  0x0802ec49 text
│   ├── strtok_r                                                                                    6   0.00%  0x080337e7 text
│   └── strtol                                                                                    232   0.13%  0x0802ef3d text
├── /                                                                                             168   0.09%  - 
│   └── opt                                                                                       168   0.09%  - 
│       └── zephyr-sdk                                                                            168   0.09%  - 
│           └── gnu                                                                               168   0.09%  - 
│               └── arm-zephyr-eabi                                                               168   0.09%  - 
│                   └── arm-zephyr-eabi                                                           168   0.09%  - 
│                       └── sys-include                                                           168   0.09%  - 
│                           ├── ssp                                                                32   0.02%  - 
│                           │   └── ssp.h                                                          32   0.02%  - 
│                           │       └── __chk_fail                                                 32   0.02%  0x080213cd text
│                           └── stdlib.h                                                          136   0.07%  - 
│                               ├── calloc                                                         52   0.03%  0x080214e5 text
│                               ├── free                                                           32   0.02%  0x080214c5 text
│                               └── malloc                                                         52   0.03%  0x08021491 text
├── OUTPUT_DIR                                                                                   1280   0.70%  - 
│   └── zephyr                                                                                   1280   0.70%  - 
│       ├── include                                                                               302   0.17%  - 
│       │   └── generated                                                                         302   0.17%  - 
│       │       └── zephyr                                                                        302   0.17%  - 
│       │           └── syscalls                                                                  302   0.17%  - 
│       │               ├── counter.h                                                              14   0.01%  - 
│       │               │   └── counter_stop.isra.0                                                14   0.01%  0x0802ff6b text
│       │               ├── flash.h                                                                16   0.01%  - 
│       │               │   └── flash_write                                                        16   0.01%  0x0803085b text
│       │               ├── kernel.h                                                               36   0.02%  - 
│       │               │   ├── k_mutex_lock.constprop.0.isra.0                                    12   0.01%  0x080315f5 text
│       │               │   ├── k_mutex_unlock.isra.0                                              12   0.01%  0x08031601 text
│       │               │   └── k_sem_give                                                         12   0.01%  0x080311e5 text
│       │               └── log_msg.h                                                             236   0.13%  - 
│       │                   ├── z_log_msg_simple_create_0                                          12   0.01%  0x0802f9bb text
│       │                   ├── z_log_msg_simple_create_0                                          12   0.01%  0x080308ab text
│       │                   ├── z_log_msg_simple_create_0                                          12   0.01%  0x0803288f text
│       │                   ├── z_log_msg_simple_create_0.constprop.0                              16   0.01%  0x08030fa5 text
│       │                   ├── z_log_msg_simple_create_0.constprop.0                              16   0.01%  0x0803123f text
│       │                   ├── z_log_msg_simple_create_1                                          12   0.01%  0x0802f815 text
│       │                   ├── z_log_msg_simple_create_1                                          12   0.01%  0x0802f9eb text
│       │                   ├── z_log_msg_simple_create_1                                          12   0.01%  0x0802f9af text
│       │                   ├── z_log_msg_simple_create_1                                          12   0.01%  0x08031d9d text
│       │                   ├── z_log_msg_simple_create_1.constprop.0                              18   0.01%  0x080310f7 text
│       │                   ├── z_log_msg_simple_create_1.constprop.0                              18   0.01%  0x08031a0f text
│       │                   ├── z_log_msg_simple_create_2.constprop.0                              28   0.02%  0x08012b25 text
│       │                   ├── z_log_msg_simple_create_2.constprop.0                              28   0.02%  0x08018245 text
│       │                   └── z_log_msg_simple_create_2.constprop.0                              28   0.02%  0x08018db5 text
│       ├── isr_tables.c                                                                          972   0.53%  - 
│       │   ├── _irq_vector_table                                                                 324   0.18%  0x08010240 rom_start
│       │   └── _sw_isr_table                                                                     648   0.35%  0x08033eb4 sw_isr_table
│       └── misc                                                                                    6   0.00%  - 
│           └── generated                                                                           6   0.00%  - 
│               └── configs.c                                                                       6   0.00%  - 
│                   └── _ConfigAbsSyms                                                              6   0.00%  0x080303f7 text
├── WORKSPACE                                                                                   55126  30.16%  - 
│   ├── Firmware                                                                                46061  25.20%  - 
│   │   ├── drivers                                                                               712   0.39%  - 
│   │   │   └── solenoid                                                                          712   0.39%  - 
│   │   │       └── solenoid.c                                                                    712   0.39%  - 
│   │   │           ├── __device_dts_ord_39                                                        32   0.02%  0x08033e34 device_area
│   │   │           ├── __devstate_dts_ord_39                                                       2   0.00%  0x2000188c device_states
│   │   │           ├── __init___device_dts_ord_39                                                  8   0.00%  0x08033b3c initlevel
│   │   │           ├── deadman_isr                                                                34   0.02%  0x0802ff49 text
│   │   │           ├── log_const_solenoid                                                          8   0.00%  0x080347c8 log_const_area
│   │   │           ├── solenoid_config_0                                                          16   0.01%  0x080351c4 rodata
│   │   │           ├── solenoid_fire                                                             196   0.11%  0x0801b835 text
│   │   │           ├── solenoid_gpios_0                                                           32   0.02%  0x080351d4 rodata
│   │   │           ├── solenoid_init                                                             348   0.19%  0x0801b6d9 text
│   │   │           └── solenoid_off                                                               36   0.02%  0x0802ff79 text
│   │   └── src                                                                                 45349  24.81%  - 
│   │       ├── calibration.c                                                                    2443   1.34%  - 
│   │       │   ├── _k_thread_data_cal_thread                                                      48   0.03%  0x080341a0 _static_thread_data_area
│   │       │   ├── _zbus_obs_data_cal_sub                                                          8   0.00%  0x2000154c datas
│   │       │   ├── _zbus_observer_fifo_cal_sub                                                    20   0.01%  0x20001a34 k_fifo_area
│   │       │   ├── cal_backing_up_entry                                                           84   0.05%  0x08013145 text
│   │       │   ├── cal_done_entry                                                                 64   0.04%  0x08012ef5 text
│   │       │   ├── cal_executing_entry                                                           460   0.25%  0x080131e9 text
│   │       │   ├── cal_load_coefficient                                                           96   0.05%  0x08012f35 text
│   │       │   ├── cal_parse_cell_key                                                             96   0.05%  0x08012e01 text
│   │       │   ├── cal_restoring_on_fail_entry                                                   100   0.05%  0x08012ffd text
│   │       │   ├── cal_save_coefficient                                                          104   0.06%  0x08012f95 text
│   │       │   ├── cal_settings_get                                                               48   0.03%  0x08012ec5 text
│   │       │   ├── cal_settings_set                                                              100   0.05%  0x08012e61 text
│   │       │   ├── cal_states                                                                     72   0.04%  0x08034f30 rodata
│   │       │   ├── cal_sub                                                                        12   0.01%  0x08034a30 zbus_observer_area
│   │       │   ├── cal_thread_fn                                                                 208   0.11%  0x08013075 text
│   │       │   ├── cal_total_absolute.isra.0                                                      80   0.04%  0x08013199 text
│   │       │   ├── cal_validating_request_entry                                                   80   0.04%  0x080133b5 text
│   │       │   ├── cal_validating_request_entry.part.0                                            20   0.01%  0x08013061 text
│   │       │   ├── calibrate_cell                                                                668   0.37%  0x08011cd9 text
│   │       │   ├── calibration_init                                                                6   0.00%  0x0802f83d text
│   │       │   ├── calibration_is_running                                                         28   0.02%  0x08013405 text
│   │       │   ├── chan_cal_requestzz0cal_sub                                                      8   0.00%  0x08034ab4 zbus_channel_observation_area
│   │       │   ├── chan_cal_requestzz0cal_sub_mask                                                 1   0.00%  0x20001a88 zbus_channel_observation_mask_area
│   │       │   ├── log_const_calibration                                                           8   0.00%  0x08034618 log_const_area
│   │       │   └── settings_handler_cal_handler                                                   24   0.01%  0x08034880 settings_handler_static_area
│   │       ├── consensus_subscriber.c                                                            216   0.12%  - 
│   │       │   ├── _k_thread_data_consensus_thread                                                48   0.03%  0x080341d0 _static_thread_data_area
│   │       │   ├── consensus_thread_fn                                                           160   0.09%  0x08012d61 text
│   │       │   └── log_const_consensus                                                             8   0.00%  0x08034650 log_const_area
│   │       ├── divecan                                                                         16334   8.94%  - 
│   │       │   ├── divecan_channels.c                                                            310   0.17%  - 
│   │       │   │   ├── _zbus_chan_data_chan_atmos_pressure                                        24   0.01%  0x20001630 datas
│   │       │   │   ├── _zbus_chan_data_chan_dive_state                                            24   0.01%  0x20001600 datas
│   │       │   │   ├── _zbus_chan_data_chan_duty_cycle                                            24   0.01%  0x200015e8 datas
│   │       │   │   ├── _zbus_chan_data_chan_setpoint                                              24   0.01%  0x20001648 datas
│   │       │   │   ├── _zbus_chan_data_chan_shutdown_request                                      24   0.01%  0x20001618 datas
│   │       │   │   ├── _zbus_chan_data_chan_solenoid_fire                                         24   0.01%  0x200015b8 datas
│   │       │   │   ├── _zbus_chan_data_chan_solenoid_status                                       24   0.01%  0x200015d0 datas
│   │       │   │   ├── _zbus_message_chan_setpoint                                                 1   0.00%  0x20001873 datas
│   │       │   │   ├── _zbus_message_chan_solenoid_status                                          1   0.00%  0x20001872 datas
│   │       │   │   ├── chan_atmos_pressure                                                        20   0.01%  0x080348f8 zbus_channel_area
│   │       │   │   ├── chan_dive_state                                                            20   0.01%  0x08034998 zbus_channel_area
│   │       │   │   ├── chan_duty_cycle                                                            20   0.01%  0x080349ac zbus_channel_area
│   │       │   │   ├── chan_setpoint                                                              20   0.01%  0x080349d4 zbus_channel_area
│   │       │   │   ├── chan_shutdown_request                                                      20   0.01%  0x080349e8 zbus_channel_area
│   │       │   │   ├── chan_solenoid_fire                                                         20   0.01%  0x080349fc zbus_channel_area
│   │       │   │   └── chan_solenoid_status                                                       20   0.01%  0x08034a10 zbus_channel_area
│   │       │   ├── divecan_ppo2_math.c                                                            74   0.04%  - 
│   │       │   │   └── divecan_set_failed_cells                                                   74   0.04%  0x0802fca7 text
│   │       │   ├── divecan_ppo2_tx.c                                                             200   0.11%  - 
│   │       │   │   ├── _k_thread_data_divecan_ppo2_tx                                             48   0.03%  0x08034200 _static_thread_data_area
│   │       │   │   ├── divecan_ppo2_tx_thread                                                    144   0.08%  0x080181b5 text
│   │       │   │   └── log_const_divecan_ppo2_tx                                                   8   0.00%  0x08034660 log_const_area
│   │       │   ├── divecan_rx.c                                                                 1927   1.05%  - 
│   │       │   │   ├── RespPing.part.0                                                           184   0.10%  0x08017b75 text
│   │       │   │   ├── _k_thread_data_divecan_rx                                                  48   0.03%  0x08034230 _static_thread_data_area
│   │       │   │   ├── _zbus_obs_data_divecan_cal_resp_listener                                    8   0.00%  0x20001660 datas
│   │       │   │   ├── bump_saturating                                                            42   0.02%  0x0802fc7d text
│   │       │   │   ├── cal_response_cb                                                           156   0.09%  0x08017ad9 text
│   │       │   │   ├── can_rx_callback                                                           132   0.07%  0x08017c2d text
│   │       │   │   ├── can_rx_msgq                                                                44   0.02%  0x20001964 k_msgq_area
│   │       │   │   ├── chan_cal_responsezz5divecan_cal_resp_listener                               8   0.00%  0x08034ad4 zbus_channel_observation_area
│   │       │   │   ├── chan_cal_responsezz5divecan_cal_resp_listener_mask                          1   0.00%  0x20001a8c zbus_channel_observation_mask_area
│   │       │   │   ├── divecan_cal_resp_listener                                                  12   0.01%  0x08034a3c zbus_observer_area
│   │       │   │   ├── divecan_rx_get_bus_id_count                                                24   0.01%  0x0801819d text
│   │       │   │   ├── divecan_rx_get_bus_init_count                                              24   0.01%  0x08018185 text
│   │       │   │   ├── divecan_rx_thread                                                          52   0.03%  0x08018151 text
│   │       │   │   ├── divecan_rx_thread.part.0                                                 1184   0.65%  0x08017cb1 text
│   │       │   │   └── log_const_divecan_rx                                                        8   0.00%  0x08034668 log_const_area
│   │       │   ├── divecan_send.c                                                                716   0.39%  - 
│   │       │   │   ├── bump_tx_count                                                              48   0.03%  0x08016c41 text
│   │       │   │   ├── divecan_send                                                              156   0.09%  0x08016d1d text
│   │       │   │   ├── divecan_send_blocking                                                     220   0.12%  0x08016db9 text
│   │       │   │   ├── divecan_send_get_tx_count                                                  24   0.01%  0x08016cad text
│   │       │   │   ├── divecan_tx_init                                                            88   0.05%  0x08016cc5 text
│   │       │   │   ├── log_const_divecan_send                                                      8   0.00%  0x08034670 log_const_area
│   │       │   │   ├── msg_to_frame                                                               96   0.05%  0x08016be1 text
│   │       │   │   ├── tx_done_callback                                                           60   0.03%  0x08016c71 text
│   │       │   │   └── tx_done_sem                                                                16   0.01%  0x20001a24 k_sem_area
│   │       │   ├── divecan_tx.c                                                                  940   0.51%  - 
│   │       │   │   ├── log_const_divecan_tx                                                        8   0.00%  0x08034678 log_const_area
│   │       │   │   ├── txCalAck                                                                   80   0.04%  0x0801718d text
│   │       │   │   ├── txCalResponse                                                              92   0.05%  0x080171dd text
│   │       │   │   ├── txCellState                                                                88   0.05%  0x08017135 text
│   │       │   │   ├── txID                                                                       72   0.04%  0x08016ee5 text
│   │       │   │   ├── txMillivolts                                                               88   0.05%  0x080170dd text
│   │       │   │   ├── txName                                                                    152   0.08%  0x08016f2d text
│   │       │   │   ├── txOBOEStat                                                                 92   0.05%  0x08017031 text
│   │       │   │   ├── txPPO2                                                                     80   0.04%  0x0801708d text
│   │       │   │   ├── txStartDevice                                                              80   0.04%  0x08016e95 text
│   │       │   │   └── txStatus                                                                  108   0.06%  0x08016fc5 text
│   │       │   ├── isotp.c                                                                      1288   0.70%  - 
│   │       │   │   ├── HandleFirstFrame.isra.0                                                   240   0.13%  0x0801737d text
│   │       │   │   ├── HandleSingleFrame.isra.0                                                  128   0.07%  0x08017239 text
│   │       │   │   ├── ISOTP_Init                                                                 92   0.05%  0x080172e9 text
│   │       │   │   ├── ISOTP_Poll                                                                 84   0.05%  0x08017679 text
│   │       │   │   ├── ISOTP_ProcessRxFrame                                                      184   0.10%  0x08017551 text
│   │       │   │   ├── ISOTP_Reset                                                                56   0.03%  0x08017345 text
│   │       │   │   ├── ISOTP_Send                                                                112   0.06%  0x08017609 text
│   │       │   │   ├── isotp_idle_entry                                                           26   0.01%  0x0802fbe9 text
│   │       │   │   ├── isotp_idle_run                                                             48   0.03%  0x0802fc0d text
│   │       │   │   ├── isotp_idle_run.part.0                                                      48   0.03%  0x080172b9 text
│   │       │   │   ├── isotp_receiving_entry                                                      10   0.01%  0x0802fc03 text
│   │       │   │   ├── isotp_receiving_run                                                       228   0.12%  0x0801746d text
│   │       │   │   ├── isotp_states                                                               24   0.01%  0x080350c0 rodata
│   │       │   │   └── log_const_isotp                                                             8   0.00%  0x08034718 log_const_area
│   │       │   ├── isotp_tx_queue.c                                                             1160   0.63%  - 
│   │       │   │   ├── ISOTP_TxQueue_Enqueue                                                     148   0.08%  0x08017969 text
│   │       │   │   ├── ISOTP_TxQueue_GetPendingCount                                              16   0.01%  0x08017ac9 text
│   │       │   │   ├── ISOTP_TxQueue_Init                                                         36   0.02%  0x08017945 text
│   │       │   │   ├── ISOTP_TxQueue_IsBusy                                                       24   0.01%  0x08017ab1 text
│   │       │   │   ├── ISOTP_TxQueue_Poll                                                         28   0.02%  0x0802fc61 text
│   │       │   │   ├── ISOTP_TxQueue_ProcessFC                                                   180   0.10%  0x080179fd text
│   │       │   │   ├── getTxSm                                                                    28   0.02%  0x080176cd text
│   │       │   │   ├── isotp_tx_msgq                                                              44   0.02%  0x200019bc k_msgq_area
│   │       │   │   ├── log_const_isotp_txq                                                         8   0.00%  0x08034720 log_const_area
│   │       │   │   ├── tx_idle_entry                                                              20   0.01%  0x0802fc3d text
│   │       │   │   ├── tx_idle_run                                                               248   0.14%  0x080176e9 text
│   │       │   │   ├── tx_states                                                                  24   0.01%  0x080350d8 rodata
│   │       │   │   └── tx_wait_fc_run                                                            356   0.19%  0x080177e1 text
│   │       │   └── uds                                                                          9719   5.32%  - 
│   │       │       ├── uds.c                                                                    2974   1.63%  - 
│   │       │       │   ├── UDS_Init                                                               80   0.04%  0x08018289 text
│   │       │       │   ├── UDS_IsInDive                                                           84   0.05%  0x080182d9 text
│   │       │       │   ├── UDS_MaintainSession                                                   120   0.07%  0x0801832d text
│   │       │       │   ├── UDS_ProcessRequest                                                   2484   1.36%  0x080183e5 text
│   │       │       │   ├── UDS_SendNegativeResponse                                               46   0.03%  0x0802fd21 text
│   │       │       │   ├── UDS_SendNegativeResponse.part.0                                        40   0.02%  0x08018261 text
│   │       │       │   ├── UDS_SendResponse                                                       64   0.04%  0x080183a5 text
│   │       │       │   ├── checkOtaWritePrecondition                                              48   0.03%  0x0802fcf1 text
│   │       │       │   └── log_const_uds                                                           8   0.00%  0x08034810 log_const_area
│   │       │       ├── uds_log_download.c                                                        844   0.46%  - 
│   │       │       │   ├── UDS_LogDownload_Claims                                                 56   0.03%  0x0801b4e9 text
│   │       │       │   ├── UDS_LogDownload_FillSelectorResult                                     64   0.04%  0x0801b365 text
│   │       │       │   ├── UDS_LogDownload_Handle                                                336   0.18%  0x0801b521 text
│   │       │       │   ├── UDS_LogDownload_HandleRoutine                                         324   0.18%  0x0801b3a5 text
│   │       │       │   ├── fl_pack_selector_result.constprop.0                                    56   0.03%  0x0801b32d text
│   │       │       │   └── log_const_uds_log_download                                              8   0.00%  0x08034818 log_const_area
│   │       │       ├── uds_log_push.c                                                            488   0.27%  - 
│   │       │       │   ├── UDS_LogPush_Init                                                       88   0.05%  0x08019f41 text
│   │       │       │   ├── UDS_LogPush_Poll                                                      140   0.08%  0x0801a069 text
│   │       │       │   ├── UDS_LogPush_SendLogMessage                                            208   0.11%  0x08019f99 text
│   │       │       │   ├── log_const_uds_log_push                                                  8   0.00%  0x08034820 log_const_area
│   │       │       │   └── log_push_msgq                                                          44   0.02%  0x200019e8 k_msgq_area
│   │       │       ├── uds_log_push_backend.c                                                    452   0.25%  - 
│   │       │       │   ├── uds_log_push_backend                                                   16   0.01%  0x08034870 log_backend_area
│   │       │       │   ├── upb_backend_api                                                        28   0.02%  0x0803516c rodata
│   │       │       │   ├── upb_data_out                                                           68   0.04%  0x0801a10d text
│   │       │       │   ├── upb_dropped                                                             6   0.00%  0x0802fdd5 text
│   │       │       │   ├── upb_format_set                                                          8   0.00%  0x0802fddb text
│   │       │       │   ├── upb_init                                                               24   0.01%  0x0801a0f5 text
│   │       │       │   ├── upb_log_output                                                         16   0.01%  0x08035188 rodata
│   │       │       │   ├── upb_panic                                                               6   0.00%  0x0802fdcf text
│   │       │       │   ├── upb_process                                                           276   0.15%  0x0801a151 text
│   │       │       │   └── upb_self_ids                                                            4   0.00%  0x20001868 datas
│   │       │       ├── uds_ota.c                                                                1798   0.98%  - 
│   │       │       │   ├── UDS_OTA_Handle                                                        100   0.05%  0x080193f5 text
│   │       │       │   ├── getOtaSm                                                               28   0.02%  0x08018d99 text
│   │       │       │   ├── log_const_uds_ota                                                       8   0.00%  0x08034828 log_const_area
│   │       │       │   ├── ota_activating_entry                                                   20   0.01%  0x0802fd65 text
│   │       │       │   ├── ota_awaiting_activate_run                                             684   0.37%  0x08018fc1 text
│   │       │       │   ├── ota_downloading_run                                                   392   0.21%  0x08018e39 text
│   │       │       │   ├── ota_downloading_run.part.0                                             52   0.03%  0x08018dd1 text
│   │       │       │   ├── ota_idle_entry                                                         22   0.01%  0x0802fd4f text
│   │       │       │   ├── ota_idle_run                                                          392   0.21%  0x0801926d text
│   │       │       │   ├── ota_states                                                             48   0.03%  0x080350f0 rodata
│   │       │       │   └── reject_sequence_error                                                  52   0.03%  0x08018e05 text
│   │       │       ├── uds_settings.c                                                           1212   0.66%  - 
│   │       │       │   ├── UDS_GetSettingCount                                                     8   0.00%  0x0802fdc7 text
│   │       │       │   ├── UDS_GetSettingInfo                                                     64   0.04%  0x08019ba1 text
│   │       │       │   ├── UDS_GetSettingOptionLabel                                              96   0.05%  0x08019ee1 text
│   │       │       │   ├── UDS_GetSettingValue                                                   168   0.09%  0x08019be1 text
│   │       │       │   ├── UDS_SaveSettingValue                                                  280   0.15%  0x08019dc9 text
│   │       │       │   ├── UDS_SetSettingValue                                                   320   0.18%  0x08019c89 text
│   │       │       │   ├── batteryTypeOptions                                                     20   0.01%  0x08035120 rodata
│   │       │       │   ├── boolOptions                                                            12   0.01%  0x08035134 rodata
│   │       │       │   ├── calModeOptions                                                         20   0.01%  0x08035140 rodata
│   │       │       │   ├── fwCommitOptions                                                         8   0.00%  0x08035164 rodata
│   │       │       │   ├── log_const_uds_settings                                                  8   0.00%  0x08034830 log_const_area
│   │       │       │   ├── ppo2ModeOptions                                                        16   0.01%  0x08035154 rodata
│   │       │       │   └── settings                                                              192   0.11%  0x08034be0 rodata
│   │       │       └── uds_state_did.c                                                          1951   1.07%  - 
│   │       │           ├── UDS_StateDID_HandleRead                                               476   0.26%  0x080199c5 text
│   │       │           ├── UDS_StateDID_IsStateDID                                                34   0.02%  0x0802fda5 text
│   │       │           ├── fillSlotVersion4                                                      108   0.06%  0x080194b5 text
│   │       │           ├── fillSlotVersion8                                                      124   0.07%  0x08019521 text
│   │       │           ├── handleControlStateDID.constprop.0                                    1062   0.58%  0x0801959d text
│   │       │           ├── kinds.0                                                                 3   0.00%  0x0803b72a rodata
│   │       │           ├── log_const_uds_state_did                                                 8   0.00%  0x08034838 log_const_area
│   │       │           ├── readBankSemVer                                                         92   0.05%  0x08019459 text
│   │       │           ├── writeFloat32                                                            8   0.00%  0x0802fd8d text
│   │       │           ├── writeInvalidVersion                                                    16   0.01%  0x0802fd95 text
│   │       │           └── writeUint32                                                            20   0.01%  0x0802fd79 text
│   │       ├── error_histogram.c                                                                 835   0.46%  - 
│   │       │   ├── HIST_SAVE_INTERVAL                                                              8   0.00%  0x08034bc8 rodata
│   │       │   ├── _zbus_obs_data_err_hist_listener                                                8   0.00%  0x20001574 datas
│   │       │   ├── chan_errorzz5err_hist_listener                                                  8   0.00%  0x08034b0c zbus_channel_observation_area
│   │       │   ├── chan_errorzz5err_hist_listener_mask                                             1   0.00%  0x20001a93 zbus_channel_observation_mask_area
│   │       │   ├── err_hist_listener                                                              12   0.01%  0x08034a54 zbus_observer_area
│   │       │   ├── error_histogram_clear                                                         132   0.07%  0x08014355 text
│   │       │   ├── error_histogram_init                                                           68   0.04%  0x080143d9 text
│   │       │   ├── error_histogram_snapshot                                                       22   0.01%  0x0802f8c5 text
│   │       │   ├── error_observer_cb                                                             116   0.06%  0x08014235 text
│   │       │   ├── hist_settings_set                                                             128   0.07%  0x080141b5 text
│   │       │   ├── log_const_err_hist                                                              8   0.00%  0x08034690 log_const_area
│   │       │   ├── save_timer                                                                     56   0.03%  0x20001900 k_timer_area
│   │       │   ├── save_timer_expiry                                                              24   0.01%  0x0801419d text
│   │       │   ├── save_work                                                                      48   0.03%  0x20000f80 datas
│   │       │   ├── save_work_handler                                                             124   0.07%  0x080142d9 text
│   │       │   ├── settings_handler_err_hist_handler                                              24   0.01%  0x08034898 settings_handler_static_area
│   │       │   └── snapshot_to_u16                                                                48   0.03%  0x080142a9 text
│   │       ├── errors.c                                                                          560   0.31%  - 
│   │       │   ├── __init_errors_init                                                              8   0.00%  0x08033b54 initlevel
│   │       │   ├── _zbus_chan_data_chan_error                                                     24   0.01%  0x20001490 datas
│   │       │   ├── chan_error                                                                     20   0.01%  0x080349c0 zbus_channel_area
│   │       │   ├── errors_get_last_crash                                                          40   0.02%  0x080125e5 text
│   │       │   ├── errors_init                                                                    32   0.02%  0x080125c5 text
│   │       │   ├── errors_init.part.0                                                            168   0.09%  0x0801251d text
│   │       │   ├── fatal_op_error                                                                 76   0.04%  0x08012655 text
│   │       │   ├── k_sys_fatal_error_handler                                                     112   0.06%  0x080126a1 text
│   │       │   ├── log_const_errors                                                                8   0.00%  0x08034698 log_const_area
│   │       │   └── op_error_publish                                                               72   0.04%  0x0801260d text
│   │       ├── factory_image.c                                                                  1924   1.05%  - 
│   │       │   ├── capture_work                                                                   16   0.01%  0x2000158c datas
│   │       │   ├── capture_work_handler                                                           56   0.03%  0x08014d51 text
│   │       │   ├── capture_work_handler.part.0                                                    92   0.05%  0x08014cf5 text
│   │       │   ├── do_capture                                                                    388   0.21%  0x08014af9 text
│   │       │   ├── ensure_work_q_started.part.0                                                  100   0.05%  0x08014a95 text
│   │       │   ├── factory_image_force_capture_async                                              52   0.03%  0x08014fb5 text
│   │       │   ├── factory_image_get_sem_ver                                                      14   0.01%  0x0802f9d5 text
│   │       │   ├── factory_image_get_version                                                      14   0.01%  0x0802f9c7 text
│   │       │   ├── factory_image_init                                                             76   0.04%  0x08014fe9 text
│   │       │   ├── factory_image_is_captured                                                      28   0.02%  0x08014f5d text
│   │       │   ├── factory_image_maybe_capture_async                                              60   0.03%  0x08014f79 text
│   │       │   ├── factory_image_read_version_field                                              136   0.07%  0x08014a0d text
│   │       │   ├── factory_image_restore_to_slot1                                                468   0.26%  0x08014d89 text
│   │       │   ├── force_capture_work                                                             16   0.01%  0x2000157c datas
│   │       │   ├── force_capture_work_handler                                                     28   0.02%  0x08014cd9 text
│   │       │   ├── force_capture_work_handler.part.0                                              92   0.05%  0x08014c7d text
│   │       │   ├── log_const_factory_image                                                         8   0.00%  0x080346a8 log_const_area
│   │       │   └── verify_first_and_last_page                                                    280   0.15%  0x080148f5 text
│   │       ├── factory_image_backend_flash.c                                                    1056   0.58%  - 
│   │       │   ├── factory_flag_settings_set                                                     108   0.06%  0x08015045 text
│   │       │   ├── factory_image_get_flash_backend                                                12   0.01%  0x08015401 text
│   │       │   ├── flash_backend                                                                  32   0.02%  0x080350a0 rodata
│   │       │   ├── flash_backend_erase                                                           120   0.07%  0x080151a5 text
│   │       │   ├── flash_backend_flush                                                             8   0.00%  0x0802f9e3 text
│   │       │   ├── flash_backend_init                                                             24   0.01%  0x0801518d text
│   │       │   ├── flash_backend_init.part.0                                                     144   0.08%  0x080150fd text
│   │       │   ├── flash_backend_is_captured                                                      16   0.01%  0x08015035 text
│   │       │   ├── flash_backend_mark_captured                                                   156   0.09%  0x0801521d text
│   │       │   ├── flash_backend_read                                                            164   0.09%  0x080152b9 text
│   │       │   ├── flash_backend_size                                                             76   0.04%  0x080150b1 text
│   │       │   ├── flash_backend_write                                                           164   0.09%  0x0801535d text
│   │       │   ├── log_const_factory_image_flash                                                   8   0.00%  0x080346b0 log_const_area
│   │       │   └── settings_handler_factory_flag_handler                                          24   0.01%  0x080348b0 settings_handler_static_area
│   │       ├── firmware_confirm.c                                                               1614   0.88%  - 
│   │       │   ├── _k_thread_data_firmware_confirm_thread                                         48   0.03%  0x08034290 _static_thread_data_area
│   │       │   ├── abort_and_reboot                                                               76   0.04%  0x08014815 text
│   │       │   ├── cell_is_alive                                                                  88   0.05%  0x0801441d text
│   │       │   ├── enter_waiting_state                                                            28   0.02%  0x0802f911 text
│   │       │   ├── firmware_confirm_get_pass_mask                                                 24   0.01%  0x08014879 text
│   │       │   ├── firmware_confirm_get_state                                                     24   0.01%  0x08014861 text
│   │       │   ├── firmware_confirm_init                                                         100   0.05%  0x08014891 text
│   │       │   ├── log_const_fw_confirm                                                            8   0.00%  0x080346e0 log_const_area
│   │       │   ├── mark_check_passed                                                              48   0.03%  0x08014495 text
│   │       │   ├── overall_deadline_exceeded                                                      36   0.02%  0x0802f8ed text
│   │       │   ├── post_cells_entry                                                               14   0.01%  0x0802f965 text
│   │       │   ├── post_cells_run                                                                120   0.07%  0x08014629 text
│   │       │   ├── post_confirmed_entry                                                          100   0.05%  0x08014555 text
│   │       │   ├── post_consensus_entry                                                           14   0.01%  0x0802f957 text
│   │       │   ├── post_consensus_run                                                            152   0.08%  0x080146a1 text
│   │       │   ├── post_failed_cell_entry                                                         10   0.01%  0x0802f99b text
│   │       │   ├── post_failed_consensus_entry                                                    10   0.01%  0x0802f991 text
│   │       │   ├── post_failed_no_handset_entry                                                   10   0.01%  0x0802f97d text
│   │       │   ├── post_failed_no_ppo2_tx_entry                                                   10   0.01%  0x0802f987 text
│   │       │   ├── post_failed_solenoid_entry                                                     10   0.01%  0x0802f973 text
│   │       │   ├── post_failed_timeout_entry                                                      10   0.01%  0x0802f9a5 text
│   │       │   ├── post_handset_entry                                                             14   0.01%  0x0802f93b text
│   │       │   ├── post_handset_run                                                              112   0.06%  0x080145b9 text
│   │       │   ├── post_ppo2_tx_entry                                                             14   0.01%  0x0802f949 text
│   │       │   ├── post_ppo2_tx_run                                                               92   0.05%  0x08014739 text
│   │       │   ├── post_solenoid_entry                                                            14   0.01%  0x0802f92d text
│   │       │   ├── post_solenoid_run                                                             144   0.08%  0x080144c5 text
│   │       │   ├── post_states                                                                   156   0.09%  0x08035004 rodata
│   │       │   └── post_thread_entry                                                             128   0.07%  0x08014795 text
│   │       ├── flash_log                                                                        4944   2.71%  - 
│   │       │   ├── flash_log.c                                                                  2769   1.52%  - 
│   │       │   │   ├── _k_thread_data_fl_writer_tid                                               48   0.03%  0x080342c0 _static_thread_data_area
│   │       │   │   ├── fl_emit_drop_marker_if_any                                                160   0.09%  0x0801a479 text
│   │       │   │   ├── fl_enqueue                                                                192   0.11%  0x0801a519 text
│   │       │   │   ├── fl_ingest_msgq                                                             44   0.02%  0x20001990 k_msgq_area
│   │       │   │   ├── fl_mount_fcb                                                              148   0.08%  0x0801a31d text
│   │       │   │   ├── fl_rtt_level                                                                1   0.00%  0x20001874 datas
│   │       │   │   ├── fl_settings_set                                                           184   0.10%  0x0801a265 text
│   │       │   │   ├── fl_write_entry_to_fcb.isra.0                                              200   0.11%  0x0801a3b1 text
│   │       │   │   ├── fl_writer_thread                                                          220   0.12%  0x0801a5d9 text
│   │       │   │   ├── flash_log_enqueue_can_rx_isr                                               96   0.05%  0x0801a6d1 text
│   │       │   │   ├── flash_log_enqueue_cell_raw                                                160   0.09%  0x0801a85d text
│   │       │   │   ├── flash_log_enqueue_consensus                                               148   0.08%  0x0801a731 text
│   │       │   │   ├── flash_log_enqueue_dive_marker                                              68   0.04%  0x0801a941 text
│   │       │   │   ├── flash_log_enqueue_error                                                    68   0.04%  0x0801a8fd text
│   │       │   │   ├── flash_log_enqueue_pid_snapshot                                             76   0.04%  0x0801a7c5 text
│   │       │   │   ├── flash_log_enqueue_solenoid_fire                                            76   0.04%  0x0801a811 text
│   │       │   │   ├── flash_log_enqueue_text                                                    120   0.07%  0x0801a985 text
│   │       │   │   ├── flash_log_erase                                                            68   0.04%  0x0801ac7d text
│   │       │   │   ├── flash_log_get_boot_id                                                      16   0.01%  0x0801ac01 text
│   │       │   │   ├── flash_log_get_can_verbose                                                  16   0.01%  0x0801abc5 text
│   │       │   │   ├── flash_log_get_rtt_level                                                    16   0.01%  0x0801ab89 text
│   │       │   │   ├── flash_log_init                                                            180   0.10%  0x0801a9fd text
│   │       │   │   ├── flash_log_internal_get_fcb                                                 28   0.02%  0x0801a6b5 text
│   │       │   │   ├── flash_log_pause                                                            36   0.02%  0x0801aab1 text
│   │       │   │   ├── flash_log_record_boot_marker                                              144   0.08%  0x0801aaf9 text
│   │       │   │   ├── flash_log_resume                                                           36   0.02%  0x0801aad5 text
│   │       │   │   ├── flash_log_set_can_verbose                                                  44   0.02%  0x0801abd5 text
│   │       │   │   ├── flash_log_set_rtt_level                                                    44   0.02%  0x0801ab99 text
│   │       │   │   ├── flash_log_stats                                                           108   0.06%  0x0801ac11 text
│   │       │   │   └── settings_handler_flash_log_settings                                        24   0.01%  0x080348c8 settings_handler_static_area
│   │       │   ├── flash_log_backend.c                                                           478   0.26%  - 
│   │       │   │   ├── fl_backend_api                                                             28   0.02%  0x08035198 rodata
│   │       │   │   ├── fl_data_out                                                                68   0.04%  0x0801ad61 text
│   │       │   │   ├── fl_dropped                                                                  6   0.00%  0x0802fe4f text
│   │       │   │   ├── fl_format_set                                                               8   0.00%  0x0802fe55 text
│   │       │   │   ├── fl_init                                                                    24   0.01%  0x0801ad49 text
│   │       │   │   ├── fl_log_output                                                              16   0.01%  0x080351b4 rodata
│   │       │   │   ├── fl_panic                                                                    6   0.00%  0x0802fe49 text
│   │       │   │   ├── fl_process                                                                300   0.16%  0x0801ada5 text
│   │       │   │   ├── fl_self_ids                                                                 6   0.00%  0x2000186c datas
│   │       │   │   └── flash_log_backend                                                          16   0.01%  0x08034850 log_backend_area
│   │       │   ├── flash_log_listeners.c                                                         345   0.19%  - 
│   │       │   │   ├── _zbus_obs_data_fl_cell_listener                                             8   0.00%  0x20001680 datas
│   │       │   │   ├── _zbus_obs_data_fl_consensus_listener                                        8   0.00%  0x20001688 datas
│   │       │   │   ├── _zbus_obs_data_fl_dive_state_listener                                       8   0.00%  0x20001678 datas
│   │       │   │   ├── _zbus_obs_data_fl_error_listener                                            8   0.00%  0x20001670 datas
│   │       │   │   ├── _zbus_obs_data_fl_solenoid_fire_listener                                    8   0.00%  0x20001668 datas
│   │       │   │   ├── cell_listener_cb                                                           22   0.01%  0x0802fde3 text
│   │       │   │   ├── chan_cell_1zz4fl_cell_listener                                              8   0.00%  0x08034adc zbus_channel_observation_area
│   │       │   │   ├── chan_cell_1zz4fl_cell_listener_mask                                         1   0.00%  0x20001a8d zbus_channel_observation_mask_area
│   │       │   │   ├── chan_cell_2zz4fl_cell_listener                                              8   0.00%  0x08034ae4 zbus_channel_observation_area
│   │       │   │   ├── chan_cell_2zz4fl_cell_listener_mask                                         1   0.00%  0x20001a8e zbus_channel_observation_mask_area
│   │       │   │   ├── chan_cell_3zz4fl_cell_listener                                              8   0.00%  0x08034aec zbus_channel_observation_area
│   │       │   │   ├── chan_cell_3zz4fl_cell_listener_mask                                         1   0.00%  0x20001a8f zbus_channel_observation_mask_area
│   │       │   │   ├── chan_consensuszz4fl_consensus_listener                                      8   0.00%  0x08034af4 zbus_channel_observation_area
│   │       │   │   ├── chan_consensuszz4fl_consensus_listener_mask                                 1   0.00%  0x20001a90 zbus_channel_observation_mask_area
│   │       │   │   ├── chan_dive_statezz4fl_dive_state_listener                                    8   0.00%  0x08034afc zbus_channel_observation_area
│   │       │   │   ├── chan_dive_statezz4fl_dive_state_listener_mask                               1   0.00%  0x20001a91 zbus_channel_observation_mask_area
│   │       │   │   ├── chan_errorzz4fl_error_listener                                              8   0.00%  0x08034b04 zbus_channel_observation_area
│   │       │   │   ├── chan_errorzz4fl_error_listener_mask                                         1   0.00%  0x20001a92 zbus_channel_observation_mask_area
│   │       │   │   ├── chan_solenoid_firezz4fl_solenoid_fire_listener                              8   0.00%  0x08034b1c zbus_channel_observation_area
│   │       │   │   ├── chan_solenoid_firezz4fl_solenoid_fire_listener_mask                         1   0.00%  0x20001a95 zbus_channel_observation_mask_area
│   │       │   │   ├── consensus_listener_cb                                                      80   0.04%  0x0801acf9 text
│   │       │   │   ├── dive_state_listener_cb                                                     32   0.02%  0x0802fdf9 text
│   │       │   │   ├── error_listener_cb                                                          26   0.01%  0x0802fe19 text
│   │       │   │   ├── fl_cell_listener                                                           12   0.01%  0x08034a60 zbus_observer_area
│   │       │   │   ├── fl_consensus_listener                                                      12   0.01%  0x08034a6c zbus_observer_area
│   │       │   │   ├── fl_dive_state_listener                                                     12   0.01%  0x08034a78 zbus_observer_area
│   │       │   │   ├── fl_error_listener                                                          12   0.01%  0x08034a84 zbus_observer_area
│   │       │   │   ├── fl_solenoid_fire_listener                                                  12   0.01%  0x08034a90 zbus_observer_area
│   │       │   │   └── solenoid_fire_listener_cb                                                  22   0.01%  0x0802fe33 text
│   │       │   └── flash_log_reader.c                                                           1352   0.74%  - 
│   │       │       ├── fl_ensure_index                                                           176   0.10%  0x0801afc5 text
│   │       │       ├── fl_index_walk_cb                                                          244   0.13%  0x0801aed1 text
│   │       │       ├── fl_range_clear                                                             22   0.01%  0x0802fe5d text
│   │       │       ├── flash_log_reader_next                                                     162   0.09%  0x0802fea7 text
│   │       │       ├── flash_log_reader_open                                                      52   0.03%  0x0802fe73 text
│   │       │       ├── flash_log_reader_resolve_boot_id                                          200   0.11%  0x0801b10d text
│   │       │       ├── flash_log_reader_resolve_dive_id                                          192   0.11%  0x0801b26d text
│   │       │       ├── flash_log_reader_resolve_latest_boot                                      152   0.08%  0x0801b075 text
│   │       │       └── flash_log_reader_resolve_latest_dive                                      152   0.08%  0x0801b1d5 text
│   │       ├── heartbeat.c                                                                       272   0.15%  - 
│   │       │   ├── heartbeat_check_all_alive                                                     144   0.08%  0x080140ed text
│   │       │   ├── heartbeat_kick                                                                 44   0.02%  0x080140c1 text
│   │       │   ├── heartbeat_register                                                             44   0.02%  0x08014095 text
│   │       │   ├── heartbeat_set_long_op                                                          32   0.02%  0x0801417d text
│   │       │   └── log_const_heartbeat                                                             8   0.00%  0x080346e8 log_const_area
│   │       ├── hw_version.c                                                                      837   0.46%  - 
│   │       │   ├── __device_dts_ord_22                                                            32   0.02%  0x08033e94 device_area
│   │       │   ├── __devstate_dts_ord_22                                                           2   0.00%  0x20001888 device_states
│   │       │   ├── __init___device_dts_ord_22                                                      8   0.00%  0x08033b4c initlevel
│   │       │   ├── hw_ver_config_0                                                                24   0.01%  0x08034f84 rodata
│   │       │   ├── hw_ver_expected_0                                                               3   0.00%  0x0803b71b rodata
│   │       │   ├── hw_ver_pins_0                                                                  24   0.01%  0x08034f9c rodata
│   │       │   ├── hw_version_init                                                               736   0.40%  0x08013605 text
│   │       │   └── log_const_hw_version                                                            8   0.00%  0x080346f0 log_const_area
│   │       ├── main.c                                                                            392   0.21%  - 
│   │       │   ├── log_const_main                                                                  8   0.00%  0x08034738 log_const_area
│   │       │   └── main                                                                          384   0.21%  0x0801239d text
│   │       ├── option_bytes.c                                                                    240   0.13%  - 
│   │       │   ├── __init_option_bytes_assert                                                      8   0.00%  0x08033b5c initlevel
│   │       │   ├── log_const_option_bytes                                                          8   0.00%  0x08034768 log_const_area
│   │       │   └── option_bytes_assert                                                           224   0.12%  0x0801540d text
│   │       ├── oxygen_cell_analog.c                                                             1025   0.56%  - 
│   │       │   ├── _k_thread_data_analog_cell_3                                                   48   0.03%  0x08034140 _static_thread_data_area
│   │       │   ├── _zbus_obs_data_analog_cal_done_listener                                         8   0.00%  0x200015a0 datas
│   │       │   ├── analog_cal_done_cb                                                             20   0.01%  0x08015789 text
│   │       │   ├── analog_cal_done_listener                                                       12   0.01%  0x08034a24 zbus_observer_area
│   │       │   ├── analog_cell_thread                                                            588   0.32%  0x0801579d text
│   │       │   ├── analog_load_cal                                                               268   0.15%  0x0801567d text
│   │       │   ├── cell_3_state                                                                   64   0.04%  0x20000fb0 datas
│   │       │   ├── chan_cal_responsezz10analog_cal_done_listener                                   8   0.00%  0x08034abc zbus_channel_observation_area
│   │       │   ├── chan_cal_responsezz10analog_cal_done_listener_mask                              1   0.00%  0x20001a89 zbus_channel_observation_mask_area
│   │       │   └── log_const_cell_analog                                                           8   0.00%  0x08034638 log_const_area
│   │       ├── oxygen_cell_channels.c                                                            524   0.29%  - 
│   │       │   ├── _zbus_chan_data_chan_cal_request                                               24   0.01%  0x200014d4 datas
│   │       │   ├── _zbus_chan_data_chan_cal_response                                              24   0.01%  0x200014bc datas
│   │       │   ├── _zbus_chan_data_chan_cell_1                                                    24   0.01%  0x20001534 datas
│   │       │   ├── _zbus_chan_data_chan_cell_2                                                    24   0.01%  0x2000151c datas
│   │       │   ├── _zbus_chan_data_chan_cell_3                                                    24   0.01%  0x20001504 datas
│   │       │   ├── _zbus_chan_data_chan_consensus                                                 24   0.01%  0x200014ec datas
│   │       │   ├── _zbus_message_chan_cal_request                                                  4   0.00%  0x20001864 datas
│   │       │   ├── _zbus_message_chan_cell_1                                                      64   0.04%  0x20000f40 datas
│   │       │   ├── _zbus_message_chan_cell_2                                                      64   0.04%  0x20000f00 datas
│   │       │   ├── _zbus_message_chan_cell_3                                                      64   0.04%  0x20000ec0 datas
│   │       │   ├── _zbus_message_chan_consensus                                                   64   0.04%  0x20000e80 datas
│   │       │   ├── chan_cal_request                                                               20   0.01%  0x08034920 zbus_channel_area
│   │       │   ├── chan_cal_response                                                              20   0.01%  0x08034934 zbus_channel_area
│   │       │   ├── chan_cell_1                                                                    20   0.01%  0x08034948 zbus_channel_area
│   │       │   ├── chan_cell_2                                                                    20   0.01%  0x0803495c zbus_channel_area
│   │       │   ├── chan_cell_3                                                                    20   0.01%  0x08034970 zbus_channel_area
│   │       │   └── chan_consensus                                                                 20   0.01%  0x08034984 zbus_channel_area
│   │       ├── oxygen_cell_diveo2.c                                                             2703   1.48%  - 
│   │       │   ├── ZBUS_PUB_TIMEOUT_MS                                                             8   0.00%  0x08034bd0 rodata
│   │       │   ├── _k_thread_data_diveo2_thread_1                                                 48   0.03%  0x08034260 _static_thread_data_area
│   │       │   ├── _zbus_obs_data_diveo2_cal_done_listener                                         8   0.00%  0x200015a8 datas
│   │       │   ├── chan_cal_responsezz10diveo2_cal_done_listener                                   8   0.00%  0x08034ac4 zbus_channel_observation_area
│   │       │   ├── chan_cal_responsezz10diveo2_cal_done_listener_mask                              1   0.00%  0x20001a8a zbus_channel_observation_mask_area
│   │       │   ├── diveo2_cal_done_cb                                                             20   0.01%  0x08015add text
│   │       │   ├── diveo2_cal_done_listener                                                       12   0.01%  0x08034a48 zbus_observer_area
│   │       │   ├── diveo2_cell_1                                                                 264   0.14%  0x20000ff0 datas
│   │       │   ├── diveo2_cell_thread                                                            220   0.12%  0x08015e4d text
│   │       │   ├── diveo2_cell_thread.part.0                                                     884   0.48%  0x08012029 text
│   │       │   ├── diveo2_format_tx_command                                                       46   0.03%  0x0802fa4f text
│   │       │   ├── diveo2_load_cal                                                               244   0.13%  0x080159e9 text
│   │       │   ├── diveo2_parse_detailed_response.part.0                                         356   0.19%  0x08015b6d text
│   │       │   ├── diveo2_parse_error_code                                                       124   0.07%  0x08015af1 text
│   │       │   ├── diveo2_parse_simple_response                                                  284   0.16%  0x08015d31 text
│   │       │   ├── diveo2_prepare_message_buffer                                                  96   0.05%  0x08015cd1 text
│   │       │   ├── diveo2_uart_callback                                                           72   0.04%  0x0802f9f7 text
│   │       │   └── log_const_cell_diveo2                                                           8   0.00%  0x08034640 log_const_area
│   │       ├── oxygen_cell_math.c                                                               1848   1.01%  - 
│   │       │   ├── analog_cal_coefficient                                                        140   0.08%  0x08012bc5 text
│   │       │   ├── analog_calculate_ppo2                                                          36   0.02%  0x08012b69 text
│   │       │   ├── analog_counts_to_mv                                                            40   0.02%  0x08012b41 text
│   │       │   ├── cal_compute_target_ppo2                                                        56   0.03%  0x08012b8d text
│   │       │   ├── consensus_calculate                                                          1272   0.70%  0x080117e1 text
│   │       │   ├── consensus_confidence                                                           24   0.01%  0x0802f7fd text
│   │       │   ├── diveo2_cal_coefficient                                                        136   0.07%  0x08012c51 text
│   │       │   ├── log_const_oxygen_cell_math                                                      8   0.00%  0x08034780 log_const_area
│   │       │   └── o2s_cal_coefficient                                                           136   0.07%  0x08012cd9 text
│   │       ├── oxygen_cell_o2s.c                                                                1705   0.93%  - 
│   │       │   ├── ZBUS_PUB_TIMEOUT_MS                                                             8   0.00%  0x08034bd8 rodata
│   │       │   ├── _k_thread_data_o2s_thread_2                                                    48   0.03%  0x080342f0 _static_thread_data_area
│   │       │   ├── _zbus_obs_data_o2s_cal_done_listener                                            8   0.00%  0x200015b0 datas
│   │       │   ├── chan_cal_responsezz10o2s_cal_done_listener                                      8   0.00%  0x08034acc zbus_channel_observation_area
│   │       │   ├── chan_cal_responsezz10o2s_cal_done_listener_mask                                 1   0.00%  0x20001a8b zbus_channel_observation_mask_area
│   │       │   ├── log_const_cell_o2s                                                              8   0.00%  0x08034648 log_const_area
│   │       │   ├── o2s_cal_done_cb                                                                20   0.01%  0x080160c9 text
│   │       │   ├── o2s_cal_done_listener                                                          12   0.01%  0x08034a9c zbus_observer_area
│   │       │   ├── o2s_cell_2                                                                     80   0.04%  0x200010f8 datas
│   │       │   ├── o2s_cell_thread                                                               220   0.12%  0x080163d5 text
│   │       │   ├── o2s_cell_thread.part.0                                                        660   0.36%  0x08016141 text
│   │       │   ├── o2s_format_tx_command                                                          46   0.03%  0x0802fac3 text
│   │       │   ├── o2s_load_cal                                                                  272   0.15%  0x08015fb9 text
│   │       │   ├── o2s_parse_response.part.0                                                     144   0.08%  0x08015f29 text
│   │       │   ├── o2s_prepare_message_buffer                                                    100   0.05%  0x080160dd text
│   │       │   └── o2s_uart_callback                                                              70   0.04%  0x0802fa7d text
│   │       ├── power_management.c                                                               2087   1.14%  - 
│   │       │   ├── __device_dts_ord_27                                                            32   0.02%  0x08033e74 device_area
│   │       │   ├── __devstate_dts_ord_27                                                           2   0.00%  0x2000188a device_states
│   │       │   ├── __init___device_dts_ord_27                                                      8   0.00%  0x08033b44 initlevel
│   │       │   ├── _k_thread_data_battery_monitor                                                 48   0.03%  0x08034170 _static_thread_data_area
│   │       │   ├── _k_thread_data_shutdown_thread                                                 48   0.03%  0x08034350 _static_thread_data_area
│   │       │   ├── _zbus_chan_data_chan_battery_status                                            24   0.01%  0x2000155c datas
│   │       │   ├── _zbus_obs_data_shutdown_sub                                                     8   0.00%  0x20001554 datas
│   │       │   ├── _zbus_observer_fifo_shutdown_sub                                               20   0.01%  0x20001a48 k_fifo_area
│   │       │   ├── battery_monitor_thread                                                        212   0.12%  0x08013d39 text
│   │       │   ├── chan_battery_status                                                            20   0.01%  0x0803490c zbus_channel_area
│   │       │   ├── chan_shutdown_requestzz0shutdown_sub                                            8   0.00%  0x08034b14 zbus_channel_observation_area
│   │       │   ├── chan_shutdown_requestzz0shutdown_sub_mask                                       1   0.00%  0x20001a94 zbus_channel_observation_mask_area
│   │       │   ├── log_const_power                                                                 8   0.00%  0x08034790 log_const_area
│   │       │   ├── power_config_0                                                                 64   0.04%  0x08034fc4 rodata
│   │       │   ├── power_get_battery_voltage                                                     216   0.12%  0x08013c61 text
│   │       │   ├── power_get_can_voltage                                                          12   0.01%  0x08013e51 text
│   │       │   ├── power_get_vbus_voltage                                                         36   0.02%  0x08013e0d text
│   │       │   ├── power_get_vcc_voltage                                                          32   0.02%  0x08013e31 text
│   │       │   ├── power_init                                                                    460   0.25%  0x08013a95 text
│   │       │   ├── power_is_can_active                                                           180   0.10%  0x08013e5d text
│   │       │   ├── power_shutdown                                                                240   0.13%  0x08013f11 text
│   │       │   ├── power_vbus_disable                                                             44   0.02%  0x0802f87f text
│   │       │   ├── sample_vcc_voltage                                                            176   0.10%  0x08011f79 text
│   │       │   ├── shutdown_sub                                                                   12   0.01%  0x08034aa8 zbus_observer_area
│   │       │   ├── shutdown_thread_fn                                                            148   0.08%  0x08014001 text
│   │       │   └── suspend_uart_if_ready                                                          28   0.02%  0x0802f853 text
│   │       ├── power_math.c                                                                       76   0.04%  - 
│   │       │   ├── adc_millivolts_to_voltage                                                      44   0.02%  0x080138e5 text
│   │       │   └── power_get_low_battery_threshold                                                32   0.02%  0x08013911 text
│   │       ├── ppo2_control.c                                                                   1492   0.82%  - 
│   │       │   ├── _k_thread_data_ppo2_pid_thread                                                 48   0.03%  0x08034320 _static_thread_data_area
│   │       │   ├── _k_thread_data_solenoid_fire_thread                                            48   0.03%  0x08034380 _static_thread_data_area
│   │       │   ├── log_const_ppo2_control                                                          8   0.00%  0x08034798 log_const_area
│   │       │   ├── ppo2_control_get_snapshot                                                      40   0.02%  0x08016a81 text
│   │       │   ├── ppo2_control_init                                                             312   0.17%  0x08016aa9 text
│   │       │   ├── ppo2_pid_thread_fn                                                            360   0.20%  0x080166d9 text
│   │       │   ├── publish_solenoid_status                                                        32   0.02%  0x0801666d text
│   │       │   ├── read_setpoint_or_default                                                       68   0.04%  0x08016629 text
│   │       │   └── solenoid_fire_thread_fn                                                       576   0.32%  0x08016841 text
│   │       ├── ppo2_control_math.c                                                               608   0.33%  - 
│   │       │   ├── pid_compute_fire_timing                                                       308   0.17%  0x080164f5 text
│   │       │   ├── pid_state_init                                                                 68   0.04%  0x080164b1 text
│   │       │   ├── pid_state_reset_dynamic                                                        24   0.01%  0x0802faf1 text
│   │       │   └── pid_update                                                                    208   0.11%  0x0802fb09 text
│   │       ├── runtime_settings.c                                                               1154   0.63%  - 
│   │       │   ├── cached.0                                                                       20   0.01%  0x200014a8 datas
│   │       │   ├── load_pid_gain                                                                  76   0.04%  0x08012769 text
│   │       │   ├── log_const_runtime_settings                                                      8   0.00%  0x080347a8 log_const_area
│   │       │   ├── pid_gain_valid                                                                 88   0.05%  0x08012711 text
│   │       │   ├── runtime_settings_get_battery_type                                              16   0.01%  0x08012b15 text
│   │       │   ├── runtime_settings_load                                                         348   0.19%  0x080128d5 text
│   │       │   ├── runtime_settings_save                                                         228   0.12%  0x08012a31 text
│   │       │   ├── runtime_settings_validate                                                      58   0.03%  0x0802f7c3 text
│   │       │   ├── settings_handler_runtime                                                       24   0.01%  0x080348e0 settings_handler_static_area
│   │       │   └── settings_set                                                                  288   0.16%  0x080127b5 text
│   │       └── watchdog_feeder.c                                                                 460   0.25%  - 
│   │           ├── _k_thread_data_watchdog_feeder                                                 48   0.03%  0x080343e0 _static_thread_data_area
│   │           ├── cached_channel_id.0                                                             4   0.00%  0x2000159c datas
│   │           ├── log_const_watchdog_feeder                                                       8   0.00%  0x08034840 log_const_area
│   │           └── watchdog_feeder_thread                                                        400   0.22%  0x080154ed text
│   ├── bootloader                                                                               1468   0.80%  - 
│   │   └── mcuboot                                                                              1468   0.80%  - 
│   │       └── boot                                                                             1468   0.80%  - 
│   │           ├── bootutil                                                                     1460   0.80%  - 
│   │           │   └── src                                                                      1460   0.80%  - 
│   │           │       └── bootutil_public.c                                                    1460   0.80%  - 
│   │           │           ├── boot_img_magic                                                     16   0.01%  0x08035b6a rodata
│   │           │           ├── boot_magic_compatible_check                                        32   0.02%  0x08032b75 text
│   │           │           ├── boot_read_flag                                                     58   0.03%  0x08032bbd text
│   │           │           ├── boot_read_image_ok                                                 20   0.01%  0x08032c0d text
│   │           │           ├── boot_read_swap_state                                              200   0.11%  0x08029341 text
│   │           │           ├── boot_read_swap_state_by_id                                         80   0.04%  0x08029409 text
│   │           │           ├── boot_set_next                                                     136   0.07%  0x080295e5 text
│   │           │           ├── boot_set_pending                                                   16   0.01%  0x08032c2f text
│   │           │           ├── boot_set_pending_multi                                             96   0.05%  0x0802966d text
│   │           │           ├── boot_swap_info_off                                                 16   0.01%  0x08032b65 text
│   │           │           ├── boot_swap_tables                                                   18   0.01%  0x0803b7ee rodata
│   │           │           ├── boot_swap_type                                                     14   0.01%  0x08032c21 text
│   │           │           ├── boot_swap_type_multi                                              316   0.17%  0x080294a9 text
│   │           │           ├── boot_write_image_ok                                                22   0.01%  0x08032bf7 text
│   │           │           ├── boot_write_magic                                                  104   0.06%  0x0802921d text
│   │           │           ├── boot_write_swap_info                                               80   0.04%  0x08029459 text
│   │           │           ├── boot_write_trailer                                                132   0.07%  0x08029285 text
│   │           │           ├── boot_write_trailer_flag                                            56   0.03%  0x08029309 text
│   │           │           ├── bootutil_buffer_is_erased                                          40   0.02%  0x08032b95 text
│   │           │           └── log_const_mcuboot_util                                              8   0.00%  0x08034748 log_const_area
│   │           └── zephyr                                                                          8   0.00%  - 
│   │               └── include                                                                     8   0.00%  - 
│   │                   └── sysflash                                                                8   0.00%  - 
│   │                       └── sysflash.h                                                          8   0.00%  - 
│   │                           └── all_slots.0                                                     8   0.00%  0x08035974 rodata
│   └── modules                                                                                  7597   4.16%  - 
│       ├── crypto                                                                               4821   2.64%  - 
│       │   └── tf-psa-crypto                                                                    4821   2.64%  - 
│       │       ├── core                                                                          910   0.50%  - 
│       │       │   ├── psa_crypto.c                                                              660   0.36%  - 
│       │       │   │   ├── mbedtls_psa_crypto_free                                                80   0.04%  0x0802e021 text
│       │       │   │   ├── mbedtls_to_psa_error                                                  160   0.09%  0x0802df81 text
│       │       │   │   ├── psa_crypto_init                                                       108   0.06%  0x0802e071 text
│       │       │   │   ├── psa_get_initialized                                                    32   0.02%  0x0802df61 text
│       │       │   │   ├── psa_hash_abort                                                         32   0.02%  0x080331c3 text
│       │       │   │   ├── psa_hash_finish                                                        48   0.03%  0x08033257 text
│       │       │   │   ├── psa_hash_setup                                                         68   0.04%  0x080331e3 text
│       │       │   │   ├── psa_hash_update                                                        48   0.03%  0x08033227 text
│       │       │   │   ├── psa_remove_key_data_from_memory                                        24   0.01%  0x0803316f text
│       │       │   │   └── psa_wipe_key_slot                                                      60   0.03%  0x08033187 text
│       │       │   ├── psa_crypto_random.c                                                       170   0.09%  - 
│       │       │   │   ├── psa_random_internal_free                                               26   0.01%  0x08033287 text
│       │       │   │   ├── psa_random_internal_init                                               52   0.03%  0x0802e0dd text
│       │       │   │   └── psa_random_internal_seed                                               92   0.05%  0x0802e111 text
│       │       │   └── psa_crypto_slot_management.c                                               80   0.04%  - 
│       │       │       ├── psa_initialize_key_slots                                               20   0.01%  0x0802e16d text
│       │       │       └── psa_wipe_all_key_slots                                                 60   0.03%  0x0802e181 text
│       │       ├── drivers                                                                      2968   1.62%  - 
│       │       │   └── builtin                                                                  2968   1.62%  - 
│       │       │       └── src                                                                  2968   1.62%  - 
│       │       │           ├── entropy.c                                                         760   0.42%  - 
│       │       │           │   ├── entropy_gather_internal.part.0                                160   0.09%  0x0802e265 text
│       │       │           │   ├── entropy_update                                                168   0.09%  0x0802e1bd text
│       │       │           │   ├── mbedtls_entropy_add_source                                     40   0.02%  0x080332c9 text
│       │       │           │   ├── mbedtls_entropy_free                                           40   0.02%  0x080332a1 text
│       │       │           │   ├── mbedtls_entropy_func                                          296   0.16%  0x0802e33d text
│       │       │           │   └── mbedtls_entropy_init                                           56   0.03%  0x0802e305 text
│       │       │           ├── entropy_poll.c                                                     76   0.04%  - 
│       │       │           │   └── mbedtls_entropy_poll_platform                                  76   0.04%  0x0802e465 text
│       │       │           ├── hmac_drbg.c                                                       632   0.35%  - 
│       │       │           │   ├── hmac_drbg_reseed_core                                         208   0.11%  0x0802e5a5 text
│       │       │           │   ├── mbedtls_hmac_drbg_free                                         28   0.02%  0x08033389 text
│       │       │           │   ├── mbedtls_hmac_drbg_init                                         22   0.01%  0x080332f1 text
│       │       │           │   ├── mbedtls_hmac_drbg_seed                                        130   0.07%  0x08033307 text
│       │       │           │   └── mbedtls_hmac_drbg_update                                      244   0.13%  0x0802e4b1 text
│       │       │           ├── psa_crypto_hash.c                                                 288   0.16%  - 
│       │       │           │   ├── mbedtls_psa_hash_abort                                         40   0.02%  0x0802e675 text
│       │       │           │   ├── mbedtls_psa_hash_finish                                       108   0.06%  0x0802e729 text
│       │       │           │   ├── mbedtls_psa_hash_setup                                        100   0.05%  0x0802e69d text
│       │       │           │   └── mbedtls_psa_hash_update                                        40   0.02%  0x0802e701 text
│       │       │           └── sha256.c                                                         1212   0.66%  - 
│       │       │               ├── K                                                             256   0.14%  0x080359b4 rodata
│       │       │               ├── mbedtls_internal_sha256_process.isra.0                        360   0.20%  0x0802e795 text
│       │       │               ├── mbedtls_sha256                                                172   0.09%  0x0802e95d text
│       │       │               ├── mbedtls_sha256_finish                                         150   0.08%  0x08033457 text
│       │       │               ├── mbedtls_sha256_free                                            22   0.01%  0x080333b5 text
│       │       │               ├── mbedtls_sha256_init                                            16   0.01%  0x080333a5 text
│       │       │               ├── mbedtls_sha256_starts                                          96   0.05%  0x0802e8fd text
│       │       │               └── mbedtls_sha256_update                                         140   0.08%  0x080333cb text
│       │       ├── extras                                                                        843   0.46%  - 
│       │       │   └── md.c                                                                      843   0.46%  - 
│       │       │       ├── mbedtls_md                                                             40   0.02%  0x080335e7 text
│       │       │       ├── mbedtls_md_finish                                                      36   0.02%  0x080335c3 text
│       │       │       ├── mbedtls_md_free                                                        62   0.03%  0x080334fb text
│       │       │       ├── mbedtls_md_get_size                                                    10   0.01%  0x0803360f text
│       │       │       ├── mbedtls_md_hmac_finish                                                128   0.07%  0x0802eb35 text
│       │       │       ├── mbedtls_md_hmac_reset                                                  46   0.03%  0x0803365b text
│       │       │       ├── mbedtls_md_hmac_setup                                                  34   0.02%  0x08033619 text
│       │       │       ├── mbedtls_md_hmac_starts                                                280   0.15%  0x0802ea1d text
│       │       │       ├── mbedtls_md_hmac_update                                                 32   0.02%  0x0803363b text
│       │       │       ├── mbedtls_md_info_from_type                                              20   0.01%  0x0802ea09 text
│       │       │       ├── mbedtls_md_init                                                        14   0.01%  0x080334ed text
│       │       │       ├── mbedtls_md_setup                                                       64   0.04%  0x08033539 text
│       │       │       ├── mbedtls_md_starts                                                      38   0.02%  0x08033579 text
│       │       │       ├── mbedtls_md_update                                                      36   0.02%  0x0803359f text
│       │       │       └── mbedtls_sha256_info                                                     3   0.00%  0x0803b822 rodata
│       │       └── platform                                                                      100   0.05%  - 
│       │           ├── platform.c                                                                 48   0.03%  - 
│       │           │   ├── mbedtls_calloc                                                         20   0.01%  0x0802ebb5 text
│       │           │   ├── mbedtls_calloc_func                                                     4   0.00%  0x20001860 datas
│       │           │   ├── mbedtls_free                                                           20   0.01%  0x0802ebc9 text
│       │           │   └── mbedtls_free_func                                                       4   0.00%  0x2000185c datas
│       │           └── platform_util.c                                                            52   0.03%  - 
│       │               ├── mbedtls_platform_zeroize                                               24   0.01%  0x0802ebdd text
│       │               ├── mbedtls_zeroize_and_free                                               24   0.01%  0x08033689 text
│       │               └── memset_func                                                             4   0.00%  0x08035ab4 rodata
│       ├── debug                                                                                 673   0.37%  - 
│       │   └── segger                                                                            673   0.37%  - 
│       │       └── SEGGER                                                                        673   0.37%  - 
│       │           └── SEGGER_RTT.c                                                              673   0.37%  - 
│       │               ├── SEGGER_RTT_HasDataUp                                                   24   0.01%  0x08029869 text
│       │               ├── SEGGER_RTT_Init                                                        48   0.03%  0x08029881 text
│       │               ├── SEGGER_RTT_Write                                                       60   0.03%  0x0802982d text
│       │               ├── SEGGER_RTT_WriteNoLock                                                 92   0.05%  0x080297d1 text
│       │               ├── SEGGER_RTT_WriteSkipNoLock                                            160   0.09%  0x08029731 text
│       │               ├── _DoInit                                                               100   0.05%  0x080296cd text
│       │               ├── _GetAvailWriteSpace                                                    22   0.01%  0x08032c3f text
│       │               ├── _WriteBlocking                                                         88   0.05%  0x08032c93 text
│       │               ├── _WriteNoCheck                                                          62   0.03%  0x08032c55 text
│       │               └── _aInitStr                                                              17   0.01%  0x0803b800 rodata
│       ├── hal                                                                                  1999   1.09%  - 
│       │   └── stm32                                                                            1999   1.09%  - 
│       │       └── stm32cube                                                                    1999   1.09%  - 
│       │           └── stm32l4xx                                                                1999   1.09%  - 
│       │               ├── drivers                                                              1931   1.06%  - 
│       │               │   ├── include                                                           905   0.50%  - 
│       │               │   │   ├── stm32l4xx_ll_dma.h                                            633   0.35%  - 
│       │               │   │   │   ├── CHANNEL_OFFSET_TAB                                          7   0.00%  0x0803b7b7 rodata
│       │               │   │   │   ├── CHANNEL_OFFSET_TAB                                          7   0.00%  0x0803b7be rodata
│       │               │   │   │   ├── CHANNEL_OFFSET_TAB                                          7   0.00%  0x0803b7e7 rodata
│       │               │   │   │   ├── LL_DMA_ClearFlag_HT1                                       10   0.01%  0x08031cb9 text
│       │               │   │   │   ├── LL_DMA_ClearFlag_HT2                                       10   0.01%  0x08031cc3 text
│       │               │   │   │   ├── LL_DMA_ClearFlag_HT3                                       12   0.01%  0x08031ccd text
│       │               │   │   │   ├── LL_DMA_ClearFlag_HT4                                       12   0.01%  0x08031cd9 text
│       │               │   │   │   ├── LL_DMA_ClearFlag_HT5                                       12   0.01%  0x08031ce5 text
│       │               │   │   │   ├── LL_DMA_ClearFlag_HT6                                       12   0.01%  0x08031cf1 text
│       │               │   │   │   ├── LL_DMA_ClearFlag_HT7                                       12   0.01%  0x08031cfd text
│       │               │   │   │   ├── LL_DMA_ClearFlag_TC1                                       10   0.01%  0x08031c69 text
│       │               │   │   │   ├── LL_DMA_ClearFlag_TC2                                       10   0.01%  0x08031c73 text
│       │               │   │   │   ├── LL_DMA_ClearFlag_TC3                                       12   0.01%  0x08031c7d text
│       │               │   │   │   ├── LL_DMA_ClearFlag_TC4                                       12   0.01%  0x08031c89 text
│       │               │   │   │   ├── LL_DMA_ClearFlag_TC5                                       12   0.01%  0x08031c95 text
│       │               │   │   │   ├── LL_DMA_ClearFlag_TC6                                       12   0.01%  0x08031ca1 text
│       │               │   │   │   ├── LL_DMA_ClearFlag_TC7                                       12   0.01%  0x08031cad text
│       │               │   │   │   ├── LL_DMA_ClearFlag_TE1                                       10   0.01%  0x08031d09 text
│       │               │   │   │   ├── LL_DMA_ClearFlag_TE2                                       10   0.01%  0x08031d13 text
│       │               │   │   │   ├── LL_DMA_ClearFlag_TE3                                       12   0.01%  0x08031d1d text
│       │               │   │   │   ├── LL_DMA_ClearFlag_TE4                                       12   0.01%  0x08031d29 text
│       │               │   │   │   ├── LL_DMA_ClearFlag_TE5                                       12   0.01%  0x08031d35 text
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
│       │               │   │       ├── LL_TIM_ClearFlag_CC2                                       12   0.01%  0x0803177f text
│       │               │   │       ├── LL_TIM_ClearFlag_CC3                                       12   0.01%  0x0803178b text
│       │               │   │       ├── LL_TIM_ClearFlag_CC4                                       12   0.01%  0x08031797 text
│       │               │   │       ├── LL_TIM_DisableIT_CC1                                       14   0.01%  0x080317b1 text
│       │               │   │       ├── LL_TIM_DisableIT_CC2                                       14   0.01%  0x080317d9 text
│       │               │   │       ├── LL_TIM_DisableIT_CC3                                       14   0.01%  0x08031801 text
│       │               │   │       ├── LL_TIM_DisableIT_CC4                                       14   0.01%  0x08031829 text
│       │               │   │       ├── LL_TIM_EnableIT_CC1                                        14   0.01%  0x080317a3 text
│       │               │   │       ├── LL_TIM_EnableIT_CC2                                        14   0.01%  0x080317cb text
│       │               │   │       ├── LL_TIM_EnableIT_CC3                                        14   0.01%  0x080317f3 text
│       │               │   │       ├── LL_TIM_EnableIT_CC4                                        14   0.01%  0x0803181b text
│       │               │   │       ├── LL_TIM_IsEnabledIT_CC1                                     12   0.01%  0x080317bf text
│       │               │   │       ├── LL_TIM_IsEnabledIT_CC2                                     12   0.01%  0x080317e7 text
│       │               │   │       ├── LL_TIM_IsEnabledIT_CC3                                     12   0.01%  0x0803180f text
│       │               │   │       ├── LL_TIM_IsEnabledIT_CC4                                     12   0.01%  0x08031837 text
│       │               │   │       ├── LL_TIM_OC_GetCompareCH1                                     8   0.00%  0x08031753 text
│       │               │   │       ├── LL_TIM_OC_GetCompareCH2                                     8   0.00%  0x0803175b text
│       │               │   │       ├── LL_TIM_OC_GetCompareCH3                                     8   0.00%  0x08031763 text
│       │               │   │       ├── LL_TIM_OC_GetCompareCH4                                     8   0.00%  0x0803176b text
│       │               │   │       ├── LL_TIM_OC_SetCompareCH1                                     8   0.00%  0x08031733 text
│       │               │   │       ├── LL_TIM_OC_SetCompareCH2                                     8   0.00%  0x0803173b text
│       │               │   │       ├── LL_TIM_OC_SetCompareCH3                                     8   0.00%  0x08031743 text
│       │               │   │       └── LL_TIM_OC_SetCompareCH4                                     8   0.00%  0x0803174b text
│       │               │   └── src                                                              1026   0.56%  - 
│       │               │       ├── stm32l4xx_hal_flash_ex.c                                      148   0.08%  - 
│       │               │       │   └── HAL_FLASHEx_OBGetConfig                                   148   0.08%  0x08028ed1 text
│       │               │       ├── stm32l4xx_hal_pwr.c                                            36   0.02%  - 
│       │               │       │   └── HAL_PWR_EnableWakeUpPin                                    36   0.02%  0x08028f65 text
│       │               │       ├── stm32l4xx_hal_pwr_ex.c                                        392   0.21%  - 
│       │               │       │   ├── HAL_PWREx_DisableInternalWakeUpLine                        20   0.01%  0x08028f89 text
│       │               │       │   ├── HAL_PWREx_EnableGPIOPullDown                              156   0.09%  0x08029039 text
│       │               │       │   ├── HAL_PWREx_EnableGPIOPullUp                                156   0.09%  0x08028f9d text
│       │               │       │   ├── HAL_PWREx_EnablePullUpPullDownConfig                       20   0.01%  0x080290d5 text
│       │               │       │   └── HAL_PWREx_EnterSHUTDOWNMode                                40   0.02%  0x080290e9 text
│       │               │       ├── stm32l4xx_hal_rcc.c                                           152   0.08%  - 
│       │               │       │   └── HAL_RCC_GetSysClockFreq                                   152   0.08%  0x08028e39 text
│       │               │       ├── stm32l4xx_ll_dma.c                                            122   0.07%  - 
│       │               │       │   ├── LL_DMA_Init                                                92   0.05%  0x08029111 text
│       │               │       │   └── LL_DMA_StructInit                                          30   0.02%  0x08032b1d text
│       │               │       └── stm32l4xx_ll_utils.c                                          176   0.10%  - 
│       │               │           └── LL_SetFlashLatency                                        176   0.10%  0x0802916d text
│       │               └── soc                                                                    68   0.04%  - 
│       │                   └── system_stm32l4xx.c                                                 68   0.04%  - 
│       │                       ├── AHBPrescTable                                                  16   0.01%  0x0803b7d7 rodata
│       │                       ├── MSIRangeTable                                                  48   0.03%  0x08035938 rodata
│       │                       └── SystemCoreClock                                                 4   0.00%  0x2000184c datas
│       ├── mbedtls                                                                                18   0.01%  - 
│       │   └── zephyr_init.c                                                                      18   0.01%  - 
│       │       └── _mbedtls_init                                                                  18   0.01%  0x08032b3b text
│       ├── mbedtls                                                                                 8   0.00%  - 
│       │   └── zephyr_init.c                                                                       8   0.00%  - 
│       │       └── __init__mbedtls_init                                                            8   0.00%  0x08033adc initlevel
│       ├── mbedtls                                                                                24   0.01%  -
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
