QuickRecon/DiveCANHead/Firmware/src/power_management.c

/**
 * @file power_management.c
 * @brief Power subsystem driver: VBUS rail control, battery voltage sampling, and shutdown.
 *
 * Implements the Zephyr driver for the `quickrecon,power-subsystem` DT-compatible node.
 * Handles enabling/disabling the VBUS regulator (with optional Rev2 power-mux steering),
 * reading battery voltage via the internal ADC, sensing CAN bus activity, and initiating
 * system shutdown. A background thread publishes periodic BatteryStatus_t updates on
 * the chan_battery_status zbus channel.
 */

#define DT_DRV_COMPAT quickrecon_power_subsystem

#include <zephyr/kernel.h>
#include <zephyr/device.h>
#include <zephyr/drivers/adc.h>
#include <zephyr/drivers/gpio.h>
#include <zephyr/drivers/hwinfo.h>
#include <zephyr/drivers/regulator.h>
#include <zephyr/drivers/sensor.h>
#include <zephyr/logging/log.h>
#include <zephyr/pm/device.h>
#include <zephyr/sys/reboot.h>
#include <zephyr/zbus/zbus.h>

#if defined(CONFIG_SOC_FAMILY_STM32)
#include <stm32l4xx_hal_pwr_ex.h>
#include <stm32l4xx_hal_rcc.h>
#include <stm32_ll_pwr.h>
#include <stm32_ll_rtc.h>
#endif

#include "divecan_channels.h"
#include "power_management.h"
#include "errors.h"
#include "common.h"
#if defined(CONFIG_FLASH_LOG)
#include "device_current.h"
#include "flash_log.h"
#endif
#if defined(CONFIG_POSEIDON_ACCESSORIES)
#include "poseidon_accessories.h"
#endif

LOG_MODULE_REGISTER(power, LOG_LEVEL_INF);

/* ---- Driver config and data ---- */

struct power_config {
    const struct device *vbus_reg;
    const struct device *battery_adc_dev;
    uint8_t battery_adc_channel;
    uint16_t battery_divider_ratio;  /* milli-units (7250 = 7.25x) */
    /* VCC sense via a sensor device (e.g. st,stm32-vbat). Reports
     * SENSOR_CHAN_VOLTAGE in volts. On Jr this also reports VBUS
     * because both rails share the regulator. */
    const struct device *vcc_sense_dev;
    bool has_vcc_sense;
    struct gpio_dt_spec can_en;
    bool has_can_en;
    struct gpio_dt_spec can_shdn;
    bool has_can_shdn;
    struct gpio_dt_spec can_silent;
    bool has_can_silent;
    /* Rev2 only */
    struct gpio_dt_spec bus_sel[2];
    bool has_bus_select;
    bool has_vbus_sense;
    bool has_can_sense;
};

struct power_data {
    int16_t batt_sample;
    struct adc_sequence batt_seq;
    bool adc_ready;
};

/* ADC resolution in bits for the STM32L4 internal ADC */
static const uint8_t ADC_RESOLUTION_BITS = 12U;

/* Fixed-point scale for logging volts as integer whole.fraction pairs.
 * Avoids pulling libc float formatting (CONFIG_CBPRINTF_FP_SUPPORT) into
 * the image, which we don't have the flash budget for. */
static const int32_t MILLIVOLTS_PER_VOLT = 1000;

/* battery_divider_ratio is stored in milli-units (7250 = 7.25x); these split
 * it into whole and two-decimal-place fraction for LOG_INF formatting. */
static const uint16_t BATTERY_DIVIDER_WHOLE_SCALE = 1000U;
static const uint16_t BATTERY_DIVIDER_FRACTION_SCALE = 10U;

/* zbus publish timeout for the periodic battery status message. */
static const uint32_t BATTERY_PUBLISH_TIMEOUT_MS = 100U;

#if defined(CONFIG_FLASH_LOG)
/**
 * @brief Capture the periodic voltage/current/gauge state in one log record.
 *
 * Runs from the battery-monitor thread, where the additional sensor reads are
 * safe to perform. Keeping them out of a synchronous zbus listener prevents a
 * slow ADC or sensor transaction from delaying every chan_battery_status
 * publisher.
 */
static void enqueue_power_snapshot(const struct device *dev,
                                   const BatteryStatus_t *battery)
{
    FlashLogPowerSnapshot_t snapshot = {
        .vbus_voltage = power_get_vbus_voltage(dev),
        .vcc_voltage = power_get_vcc_voltage(dev),
        .battery_voltage = battery->voltage,
        .can_voltage = power_get_can_voltage(dev),
        .battery_threshold = battery->threshold,
        .current_ua = 0,
        .current_age_ms = UINT32_MAX,
        .poseidon_age_seconds = UINT16_MAX,
        .poseidon_percent = UINT8_MAX,
        .flags = 0U,
    };

    if (snapshot.battery_voltage >= 0.0f) {
        snapshot.flags |= FL_POWER_BATTERY_VALID;
    }
    if (snapshot.vbus_voltage >= 0.0f) {
        snapshot.flags |= FL_POWER_VBUS_VALID;
    }
    if (snapshot.vcc_voltage >= 0.0f) {
        snapshot.flags |= FL_POWER_VCC_VALID;
    }
    if (snapshot.can_voltage >= 0.0f) {
        snapshot.flags |= FL_POWER_CAN_VALID;
    }
    if (battery->low_battery) {
        snapshot.flags |= FL_POWER_LOW_BATTERY;
    }
    if (device_current_read(&snapshot.current_ua, &snapshot.current_age_ms)) {
        snapshot.flags |= FL_POWER_CURRENT_VALID;
    }

#if defined(CONFIG_POSEIDON_ACCESSORIES)
    PoseidonGaugeStatus_t gauge = {0};
    poseidon_gauge_status(&gauge);
    snapshot.poseidon_age_seconds = gauge.age_seconds;
    if (gauge.ever_received) {
        snapshot.poseidon_percent = gauge.percent;
        snapshot.flags |= FL_POWER_POSEIDON_PERCENT_VALID;
    }
    if (gauge.fresh) {
        snapshot.flags |= FL_POWER_POSEIDON_PERCENT_FRESH;
    }
#endif

    flash_log_enqueue_power_snapshot(&snapshot);
}
#endif

#if defined(CONFIG_SOC_FAMILY_STM32)
/* STM32L4 reports a CAN_EN SHUTDOWN wake on this rig as PIN|BROWNOUT rather
 * than RESET_LOW_POWER_WAKE. A backup-domain marker set immediately before
 * SHUTDOWN lets startup distinguish that intentional wake from an ordinary
 * cold/reset boot with the same hwinfo signature.
 */
#define SHUTDOWN_WAKE_MARKER_REG LL_RTC_BKP_DR31
#define SHUTDOWN_WAKE_MARKER     0x5152574bU /* "QRWK" */
#endif

/* ---- ADC voltage sampling ---- */

/**
 * @brief Read the battery voltage by performing an ADC conversion and applying the resistor-divider ratio.
 *
 * @param cfg Driver config containing ADC device handle, channel, and divider ratio.
 * @param data Driver data holding the ADC sequence state and sample buffer.
 * @return Battery voltage in volts, or -1.0 if the ADC is not ready or the conversion failed.
 */
static Numeric_t sample_battery_voltage(const struct power_config *cfg,
                    struct power_data *data)
{
    Numeric_t result = -1.0f;

    if (data->adc_ready) {
        data->batt_seq.buffer = &data->batt_sample;
        data->batt_seq.buffer_size = sizeof(data->batt_sample);

        Status_t ret = adc_read(cfg->battery_adc_dev, &data->batt_seq);

        if (0 == ret) {
            /* Convert raw 12-bit ADC value to millivolts using internal VREF.
             * The STM32L4 internal ADC uses a 3.0V reference at 12-bit resolution.
             * Then apply the external resistor divider ratio to get real voltage. */
            int32_t mv = data->batt_sample;

            (void)adc_raw_to_millivolts(adc_ref_internal(cfg->battery_adc_dev),
                            ADC_GAIN_1, ADC_RESOLUTION_BITS, &mv);

            result = adc_millivolts_to_voltage(mv, cfg->battery_divider_ratio);
        } else {
            OP_ERROR_DETAIL(OP_ERR_INT_ADC, (uint32_t)ret);
        }
    }

    return result;
}

/**
 * @brief Read the VCC rail voltage from the configured sensor device.
 *
 * Wraps `sensor_sample_fetch` + `sensor_channel_get` for the VCC sense
 * sensor (typically `st,stm32-vbat`). The sensor driver applies the
 * chip's internal divider so the returned value is the regulated VCC
 * voltage in volts.
 *
 * @param cfg Driver config; cfg->has_vcc_sense must be true.
 * @return VCC voltage in volts, or -1.0 if the sensor read failed.
 */
static Numeric_t sample_vcc_voltage(const struct power_config *cfg)
{
    Numeric_t result = -1.0f;
    struct sensor_value val = {0};

    Status_t fetch_ret = sensor_sample_fetch_chan(cfg->vcc_sense_dev,
                              SENSOR_CHAN_VOLTAGE);
    if (0 != fetch_ret) {
        OP_ERROR_DETAIL(OP_ERR_INT_ADC, (uint32_t)fetch_ret);
    } else {
        Status_t get_ret = sensor_channel_get(cfg->vcc_sense_dev,
                              SENSOR_CHAN_VOLTAGE, &val);
        if (0 != get_ret) {
            OP_ERROR_DETAIL(OP_ERR_INT_ADC, (uint32_t)get_ret);
        } else {
            /* Float variant on purpose: sensor_value_to_double() was the
             * last double-arithmetic caller in the image and alone pulled
             * ~2 KB of soft-double libgcc onto this FPU-less build. µV
             * resolution on a VBAT divider reading is far below the ADC's
             * own error, so float precision is ample. */
            result = sensor_value_to_float(&val);
        }
    }

    return result;
}

/* ---- Public API ---- */

/**
 * @brief Drive a GPIO and report a non-fatal error if the write fails.
 *
 * Wraps gpio_pin_set_dt() so HAL-layer failures on the power-mux and
 * CAN-control pins surface on the error channel instead of being silently
 * dropped. Thread-context (runtime) use only — never call from an ISR.
 *
 * @param spec  GPIO to drive.
 * @param value Logical level to write.
 */
static void set_gpio_checked(const struct gpio_dt_spec *spec, int32_t value)
{
    Status_t ret = gpio_pin_set_dt(spec, value);

    if (0 != ret) {
        OP_ERROR_DETAIL(OP_ERR_GPIO, (uint32_t)(-ret));
    }
}

/**
 * @brief Enable the VBUS regulator, optionally configuring the Rev2 power-mux first.
 *
 * On Rev2 hardware the bus_sel GPIOs are set according to the compiled power mode
 * (BATTERY, BATTERY_THEN_CAN, or CAN) before the regulator is turned on.
 *
 * @param dev Power subsystem device handle.
 * @return 0 on success, negative errno from the regulator driver on failure.
 */
Status_t power_vbus_enable(const struct device *dev)
{
    const struct power_config *cfg = dev->config;

    /* If we have a bus select mux (Rev2), set it according to the
     * configured power mode before enabling the regulator.
     * These values are specifically chosen to match up with the IO of the
     * power muxes:
     *   00 = battery only
     *   01 = battery then CAN fallback
     *   10 = CAN only
     *   11 = off (shutdown) */
    if (cfg->has_bus_select) {
#if defined(CONFIG_POWER_MODE_BATTERY)
        set_gpio_checked(&cfg->bus_sel[0], 0);
        set_gpio_checked(&cfg->bus_sel[1], 0);
#elif defined(CONFIG_POWER_MODE_BATTERY_THEN_CAN)
        set_gpio_checked(&cfg->bus_sel[0], 1);
        set_gpio_checked(&cfg->bus_sel[1], 0);
#elif defined(CONFIG_POWER_MODE_CAN)
        set_gpio_checked(&cfg->bus_sel[0], 0);
        set_gpio_checked(&cfg->bus_sel[1], 1);
#endif
    }

    return regulator_enable(cfg->vbus_reg);
}

/**
 * @brief Disable the VBUS regulator and, on Rev2, drive bus_sel to MODE_OFF (11).
 *
 * @param dev Power subsystem device handle.
 * @return 0 on success, negative errno from the regulator driver on failure.
 */
Status_t power_vbus_disable(const struct device *dev)
{
    const struct power_config *cfg = dev->config;

    Status_t ret = regulator_disable(cfg->vbus_reg);

    /* If we have a bus select mux (Rev2), set both high to select
     * MODE_OFF (11) to fully disconnect the mux */
    if (cfg->has_bus_select) {
        set_gpio_checked(&cfg->bus_sel[0], 1);
        set_gpio_checked(&cfg->bus_sel[1], 1);
    }

    return ret;
}

/**
 * @brief Query whether the VBUS regulator is currently enabled.
 *
 * @param dev Power subsystem device handle.
 * @return true if the regulator reports it is enabled, false otherwise.
 */
bool power_vbus_is_enabled(const struct device *dev)
{
    const struct power_config *cfg = dev->config;

    return regulator_is_enabled(cfg->vbus_reg);
}

/**
 * @brief Read the current battery voltage.
 *
 * @param dev Power subsystem device handle.
 * @return Battery voltage in volts, or -1.0 if the ADC is unavailable.
 */
Numeric_t power_get_battery_voltage(const struct device *dev)
{
    const struct power_config *cfg = dev->config;
    struct power_data *data = dev->data;

    return sample_battery_voltage(cfg, data);
}

/**
 * @brief Read the current VBUS rail voltage.
 *
 * On Jr, VBUS shares a regulator with VCC so this reads the VCC sense
 * (the STM32 internal VBAT sensor monitoring VDD). On Rev2 — which has a
 * dedicated VBUS sense ADC channel — this will read that channel directly
 * once the Rev2 path is implemented.
 *
 * @param dev Power subsystem device handle.
 * @return VBUS voltage in volts, or -1.0 if unavailable.
 */
Numeric_t power_get_vbus_voltage(const struct device *dev)
{
    const struct power_config *cfg = dev->config;
    Numeric_t result = -1.0f;

    if (cfg->has_vbus_sense) {
        /* TODO(aren.leishman@gmail.com): Rev2 path — read vbus-sense-io-channels, target 2026-05-11 */
    } else if (cfg->has_vcc_sense) {
        /* Jr: VBUS == VCC physically (shared regulator), so reading the
         * VCC sensor is the most accurate VBUS measurement available. */
        result = sample_vcc_voltage(cfg);
    } else {
        /* No sense hardware on this variant — leave at -1.0 sentinel. */
    }

    return result;
}

/**
 * @brief Read the current VCC rail voltage.
 *
 * Reads the configured VCC sense sensor (on Jr, the STM32 internal VBAT
 * sensor monitoring VDD through the chip's 1/3 divider).
 *
 * @param dev Power subsystem device handle.
 * @return VCC voltage in volts, or -1.0 if no VCC sense hardware is configured.
 */
Numeric_t power_get_vcc_voltage(const struct device *dev)
{
    const struct power_config *cfg = dev->config;
    Numeric_t result = -1.0f;

    if (cfg->has_vcc_sense) {
        result = sample_vcc_voltage(cfg);
    }

    return result;
}

/**
 * @brief Read the CAN bus supply voltage.
 *
 * Only available on Rev2 hardware with can-sense-io-channels defined.
 * Returns -1.0 on Jr (no CAN sense hardware present).
 *
 * @param dev Power subsystem device handle.
 * @return CAN supply voltage in volts, or -1.0 if unavailable.
 */
Numeric_t power_get_can_voltage(const struct device *dev)
{
    const struct power_config *cfg = dev->config;
    Numeric_t result = -1.0f;

    if (cfg->has_can_sense) {
        /* TODO(aren.leishman@gmail.com): Rev2 path — read can-sense-io-channels, target 2026-05-11 */
    } else {
        /* No CAN sense hardware on Jr; return unavailable sentinel */
    }

    return result;
}

/**
 * @brief Check whether the DiveCAN bus is currently active (dive computer present and powered).
 *
 * The CAN_EN pin is active-low: a LOW level means the bus is on. A pull-up is
 * momentarily applied to discharge capacitive coupling before sampling, then
 * removed to minimise quiescent current.
 *
 * @param dev Power subsystem device handle.
 * @return true if the CAN bus is active, false if not present or no CAN_EN GPIO.
 */
bool power_is_can_active(const struct device *dev)
{
    const struct power_config *cfg = dev->config;
    bool active = false;

    if (cfg->has_can_en) {
        /* Pull up the GPIO pin to avoid capacitance giving a false active */
        Status_t cfg_ret = gpio_pin_configure_dt(&cfg->can_en,
                                 GPIO_INPUT | GPIO_PULL_UP);

        if (0 != cfg_ret) {
            OP_ERROR_DETAIL(OP_ERR_GPIO, (uint32_t)(-cfg_ret));
        }

        /* CAN_EN is active-low: pin LOW means bus is active. A negative
         * errno here must not be mistaken for a non-zero (active) level. */
        Status_t level = gpio_pin_get_dt(&cfg->can_en);

        if (level < 0) {
            OP_ERROR_DETAIL(OP_ERR_GPIO, (uint32_t)(-level));
        } else {
            active = (0 != level);
        }

        /* Return to no pull to save power */
        cfg_ret = gpio_pin_configure_dt(&cfg->can_en, GPIO_INPUT);
        if (0 != cfg_ret) {
            OP_ERROR_DETAIL(OP_ERR_GPIO, (uint32_t)(-cfg_ret));
        }
    }

    return active;
}

#if defined(CONFIG_SOC_FAMILY_STM32)
static void stm32_backup_domain_access_begin(bool *rtcapb_was_enabled,
                         bool *backup_was_enabled)
{
    *rtcapb_was_enabled = (0U != __HAL_RCC_RTCAPB_IS_CLK_ENABLED());
    *backup_was_enabled = (0U != LL_PWR_IsEnabledBkUpAccess());

    __HAL_RCC_RTCAPB_CLK_ENABLE();
    LL_PWR_EnableBkUpAccess();
}

static void stm32_backup_domain_access_end(bool rtcapb_was_enabled,
                       bool backup_was_enabled)
{
    if (!backup_was_enabled) {
        LL_PWR_DisableBkUpAccess();
    }
    if (!rtcapb_was_enabled) {
        __HAL_RCC_RTCAPB_CLK_DISABLE();
    }
}

static void stm32_shutdown_wake_marker_set(void)
{
    bool rtcapb_was_enabled = false;
    bool backup_was_enabled = false;

    stm32_backup_domain_access_begin(&rtcapb_was_enabled, &backup_was_enabled);
    LL_RTC_BAK_SetRegister(RTC, SHUTDOWN_WAKE_MARKER_REG,
                   SHUTDOWN_WAKE_MARKER);
    stm32_backup_domain_access_end(rtcapb_was_enabled, backup_was_enabled);
}

static bool stm32_shutdown_wake_marker_consume(void)
{
    bool rtcapb_was_enabled = false;
    bool backup_was_enabled = false;

    stm32_backup_domain_access_begin(&rtcapb_was_enabled, &backup_was_enabled);
    bool marker_present =
        (SHUTDOWN_WAKE_MARKER ==
         LL_RTC_BAK_GetRegister(RTC, SHUTDOWN_WAKE_MARKER_REG));
    if (marker_present) {
        LL_RTC_BAK_SetRegister(RTC, SHUTDOWN_WAKE_MARKER_REG, 0U);
    }
    stm32_backup_domain_access_end(rtcapb_was_enabled, backup_was_enabled);

    return marker_present;
}
#endif

bool power_reset_requires_can_enable_check(uint32_t reset_cause)
{
    bool requires_check = (0U != (reset_cause & RESET_LOW_POWER_WAKE));

#if defined(CONFIG_SOC_FAMILY_STM32)
    if (!requires_check &&
        ((RESET_PIN | RESET_BROWNOUT) ==
         (reset_cause & (RESET_PIN | RESET_BROWNOUT)))) {
        requires_check = stm32_shutdown_wake_marker_consume();
    }
#endif

    return requires_check;
}

Status_t power_can_enable_assert(const struct device *dev)
{
    const struct power_config *cfg = dev->config;
    Status_t result = -ENODEV;

    if (cfg->has_can_en) {
        /* can_en is GPIO_ACTIVE_LOW, so logical ACTIVE drives physical LOW.
         * We never drive the shared line high: release changes it back to an
         * input, avoiding contention with the handset. */
        result = gpio_pin_configure_dt(&cfg->can_en, GPIO_OUTPUT_ACTIVE);
        if (0 != result) {
            OP_ERROR_DETAIL(OP_ERR_GPIO, (uint32_t)(-result));
        }
    }

    return result;
}

Status_t power_can_enable_release(const struct device *dev)
{
    const struct power_config *cfg = dev->config;
    Status_t result = -ENODEV;

    if (cfg->has_can_en) {
        result = gpio_pin_configure_dt(&cfg->can_en, GPIO_INPUT);
        if (0 != result) {
            OP_ERROR_DETAIL(OP_ERR_GPIO, (uint32_t)(-result));
        }
    }

    return result;
}

#if defined(CONFIG_SOC_FAMILY_STM32)
/**
 * @brief Suspend a UART device if it's bound and ready.
 *
 * Helper for the cell-UART deinit step of power_shutdown(). Treats
 * unready devices and suspend failures as benign — the goal is to
 * get into SHUTDOWN, and a UART that wasn't resumed in the first
 * place doesn't matter.
 */
/* __maybe_unused: an all-analog binary (e.g. eCCR_classic) disables every cell
 * USART, so there are no call sites and -Werror=unused-function would fail. */
__maybe_unused static void suspend_uart_if_ready(const struct device *dev)
{
    if (true == device_is_ready(dev)) {
        (void)pm_device_action_run(dev, PM_DEVICE_ACTION_SUSPEND);
    }
}
#endif

/**
 * @brief Enter the lowest available power state, awaiting a DiveCAN bus wakeup.
 *
 * Silences the CAN transceiver, disables VBUS, suspends the cell UARTs,
 * configures GPIO pulls for minimal leakage, then enters STM32 SHUTDOWN
 * with PWR_WAKEUP_PIN2 (PC13 = CAN_EN, active-low) armed. From SHUTDOWN
 * the SoC draws <1 µA on the L431; CAN traffic re-asserting CAN_EN low
 * triggers a low-power wake reset and the firmware validates that wake before
 * continuing the normal boot sequence.
 *
 * Falls back to sys_reboot() if the HAL entry returns or on non-STM32
 * targets (so native_sim test fixtures don't fault).
 *
 * @param dev Power subsystem device handle.
 * @return Never returns; HAL SHUTDOWN entry or sys_reboot() take over.
 */
Status_t power_shutdown(const struct device *dev)
{
    const struct power_config *cfg = dev->config;

    LOG_INF("Entering shutdown");

    /* CAN_EN is held physically low while the application is running. It
     * must be high impedance before the SHUTDOWN pull-up and WKUP2_LOW take
     * ownership. This is idempotent when the shutdown worker already released
     * it before sending accessory shutdown commands. */
    (void)power_can_enable_release(dev);

    /* Step 1: put the CAN transceiver into listen-only before doing anything
     * else so the bus sees a clean idle state. Assert the silent line (drives
     * the TCAN334 S pin high); the PWR pull-up armed in step 4 then holds it
     * through sleep. can_shdn is left inactive here — the shutdown pull in
     * step 4 raises SHDN to fully power the transceiver down. */
    if (cfg->has_can_silent) {
        set_gpio_checked(&cfg->can_silent, 1);
    }
    if (cfg->has_can_shdn) {
        set_gpio_checked(&cfg->can_shdn, 0);
    }

    /* Step 2: drop VBUS — peripherals lose power. */
    (void)power_vbus_disable(dev);

#if defined(CONFIG_SOC_FAMILY_STM32)
    /* Step 3: suspend the cell UARTs so their pins stop being driven.
     * The pins still need pull-up below to stop digital cells from
     * dropping into analog mode, but the controller has to release
     * them first. */
#if DT_NODE_HAS_STATUS(DT_NODELABEL(usart1), okay)
    suspend_uart_if_ready(DEVICE_DT_GET(DT_NODELABEL(usart1)));
#endif
#if DT_NODE_HAS_STATUS(DT_NODELABEL(usart2), okay)
    suspend_uart_if_ready(DEVICE_DT_GET(DT_NODELABEL(usart2)));
#endif
#if DT_NODE_HAS_STATUS(DT_NODELABEL(usart3), okay)
    suspend_uart_if_ready(DEVICE_DT_GET(DT_NODELABEL(usart3)));
#endif

    /* Step 4: arm GPIO pulls (Standby/Shutdown PUPDR registers) so
     * floating inputs don't bleed current. The pin map is intentionally
     * Jr-specific — see divecan_jr.dts for the authoritative pin
     * assignments. Pull tables for new boards must be re-derived from
     * their own DTS; do not assume Rev1 legacy pulls translate. */
    HAL_PWREx_EnablePullUpPullDownConfig();

    /* CAN transceiver: SHDN high (off), SILENT high (recessive). */
    (void)HAL_PWREx_EnableGPIOPullUp(PWR_GPIO_C, PWR_GPIO_BIT_14);
    (void)HAL_PWREx_EnableGPIOPullUp(PWR_GPIO_C, PWR_GPIO_BIT_15);

    /* VBUS regulator enable (PA1) low — keep VBUS off through wake. */
    (void)HAL_PWREx_EnableGPIOPullDown(PWR_GPIO_A, PWR_GPIO_BIT_1);

    /* Solenoid drives (PB4, PB5, PA7, PC11) low — fail-safe off. */
    (void)HAL_PWREx_EnableGPIOPullDown(PWR_GPIO_B, PWR_GPIO_BIT_4);
    (void)HAL_PWREx_EnableGPIOPullDown(PWR_GPIO_B, PWR_GPIO_BIT_5);
    (void)HAL_PWREx_EnableGPIOPullDown(PWR_GPIO_A, PWR_GPIO_BIT_7);
    (void)HAL_PWREx_EnableGPIOPullDown(PWR_GPIO_C, PWR_GPIO_BIT_11);

    /* O2S/DiveO2 UART pins: pull up RX/TX so cells don't fall into
     * analog mode (legacy footnote — only matters for O2S, but pulling
     * up an idling UART is harmless for analog/DiveO2). */
#if defined(CONFIG_CELL_1_TYPE_O2S) || defined(CONFIG_CELL_1_TYPE_DIVEO2)
    (void)HAL_PWREx_EnableGPIOPullUp(PWR_GPIO_B, PWR_GPIO_BIT_6);
    (void)HAL_PWREx_EnableGPIOPullUp(PWR_GPIO_B, PWR_GPIO_BIT_7);
#endif
#if (defined(CONFIG_CELL_2_TYPE_O2S) || defined(CONFIG_CELL_2_TYPE_DIVEO2)) && \
    (CONFIG_CELL_COUNT >= 2)
    (void)HAL_PWREx_EnableGPIOPullUp(PWR_GPIO_A, PWR_GPIO_BIT_2);
    (void)HAL_PWREx_EnableGPIOPullUp(PWR_GPIO_A, PWR_GPIO_BIT_3);
#endif
#if (defined(CONFIG_CELL_3_TYPE_O2S) || defined(CONFIG_CELL_3_TYPE_DIVEO2)) && \
    (CONFIG_CELL_COUNT >= 3)
    (void)HAL_PWREx_EnableGPIOPullUp(PWR_GPIO_C, PWR_GPIO_BIT_4);
    (void)HAL_PWREx_EnableGPIOPullUp(PWR_GPIO_C, PWR_GPIO_BIT_5);
#endif

    /* CAN_EN (PC13) is the wakeup line. Pull it up so the unit
     * idles high; CAN traffic asserts low → WKUP2_LOW fires →
     * power-on reset. */
    (void)HAL_PWREx_EnableGPIOPullUp(PWR_GPIO_C, PWR_GPIO_BIT_13);

    /* Step 5: arm wakeup and clear stale flags. */
    __disable_irq();
    (void)__HAL_PWR_CLEAR_FLAG(PWR_FLAG_WUF1);
    (void)__HAL_PWR_CLEAR_FLAG(PWR_FLAG_WUF2);
    (void)__HAL_PWR_CLEAR_FLAG(PWR_FLAG_WUF3);
    (void)__HAL_PWR_CLEAR_FLAG(PWR_FLAG_WUF4);
    (void)__HAL_PWR_CLEAR_FLAG(PWR_FLAG_WUF5);

    HAL_PWR_EnableWakeUpPin(PWR_WAKEUP_PIN2_LOW);
    HAL_PWREx_DisableInternalWakeUpLine();
    stm32_shutdown_wake_marker_set();

    /* Step 6: SHUTDOWN. Does not return on success — wakeup is a reset. */
    HAL_PWREx_EnterSHUTDOWNMode();
#endif /* CONFIG_SOC_FAMILY_STM32 */

    /* Hard fallback — only reached if HAL entry returns (shouldn't on
     * STM32) or on native_sim where the HAL is absent. */
    LOG_ERR("SHUTDOWN entry returned, falling back to sys_reboot");
    sys_reboot(SYS_REBOOT_COLD);

    CODE_UNREACHABLE;
    return 0;
}

/* ---- Driver init ---- */

#if defined(CONFIG_SOC_FAMILY_STM32)
/**
 * @brief Release the STM32 Standby/Shutdown GPIO pull configuration latched on the way into shutdown.
 *
 * power_shutdown() arms PWR_PUCRx/PWR_PDCRx pulls (via APC) so the CAN
 * transceiver control lines hold a safe state while the SoC sleeps. Those
 * registers live in the always-on VDD domain: on this board VCC never drops,
 * so waking from SHUTDOWN does NOT reset them. Left applied, the retained
 * pull-up on the transceiver silent line (PC15) overrides the TCAN334's
 * internal pull-down and holds it in listen-only mode — the head powers up
 * but can neither ACK nor transmit, so the handset reports "no connection".
 * A cold boot never sees this because a true power-on reset clears the PWR
 * block. Clearing APC here neutralises every latched pull; the individual
 * CAN pins are cleared explicitly too so the PUCR bits themselves are reset.
 */
static void clear_standby_pull_config(void)
{
    (void)HAL_PWREx_DisableGPIOPullUp(PWR_GPIO_C, PWR_GPIO_BIT_13);
    (void)HAL_PWREx_DisableGPIOPullUp(PWR_GPIO_C, PWR_GPIO_BIT_14);
    (void)HAL_PWREx_DisableGPIOPullUp(PWR_GPIO_C, PWR_GPIO_BIT_15);
    HAL_PWREx_DisablePullUpPullDownConfig();
}
#endif

/**
 * @brief Set up the battery voltage ADC channel and conversion sequence.
 *
 * Non-fatal if the ADC device isn't ready or channel setup fails — voltage
 * reads simply return -1.0 via the data->adc_ready gate in
 * sample_battery_voltage(). Split out of power_init() to keep that
 * function's cognitive complexity within the project limit.
 *
 * @param cfg Driver config containing the ADC device handle and channel.
 * @param data Driver data; adc_ready and batt_seq are populated on success.
 */
static void setup_battery_adc(const struct power_config *cfg, struct power_data *data)
{
    data->adc_ready = false;

    if (true == device_is_ready(cfg->battery_adc_dev)) {
        struct adc_channel_cfg ch_cfg = {
            .gain = ADC_GAIN_1,
            .reference = ADC_REF_INTERNAL,
            .acquisition_time = ADC_ACQ_TIME_MAX,
            .channel_id = cfg->battery_adc_channel,
            .differential = 0,
#if defined(CONFIG_ADC_CONFIGURABLE_INPUTS)
            /* Pulled in globally by the ADS1x1x external-ADC driver on
             * variants that have one; this internal-ADC channel has no
             * selectable input pair, so both are left at 0. */
            .input_positive = 0,
            .input_negative = 0,
#endif
        };

        Status_t adc_ret = adc_channel_setup(cfg->battery_adc_dev, &ch_cfg);

        if (0 == adc_ret) {
            data->batt_seq.channels = BIT(cfg->battery_adc_channel);
            data->batt_seq.resolution = ADC_RESOLUTION_BITS;
            data->batt_seq.oversampling = 0;
            data->batt_seq.buffer = &data->batt_sample;
            data->batt_seq.buffer_size = sizeof(data->batt_sample);
            data->adc_ready = true;
        } else {
            LOG_WRN("Battery ADC setup failed: %d (voltage reads disabled)",
                adc_ret);
        }
    } else {
        LOG_WRN("Battery ADC not ready (voltage reads disabled)");
    }
}

/**
 * @brief Configure the CAN enable/shutdown/silent GPIOs and, on Rev2, the bus-select mux.
 *
 * Each GPIO is configured only if present in cfg; the first configuration
 * failure short-circuits the remaining steps. Split out of power_init() to
 * keep that function's cognitive complexity within the project limit.
 *
 * @param cfg Driver config containing the optional CAN control GPIOs.
 * @return 0 on success, negative errno from the first failing gpio_pin_configure_dt() call.
 */
static Status_t configure_can_gpios(const struct power_config *cfg)
{
    Status_t result = 0;

    if (cfg->has_can_en) {
        result = gpio_pin_configure_dt(&cfg->can_en, GPIO_INPUT);
        if (0 != result) {
            LOG_ERR("CAN enable GPIO config failed: %d", result);
        }
    }

    /* Configure CAN silent output if present. Driven INACTIVE (silent
     * line low → transceiver in normal mode). A push-pull output holds
     * this regardless of the TCAN334's internal pull-down or any pull
     * left over from a previous shutdown, so the bus comes up on every
     * boot — cold or warm. */
    if ((0 == result) && cfg->has_can_shdn) {
        result = gpio_pin_configure_dt(&cfg->can_shdn, GPIO_OUTPUT_INACTIVE);
        if (0 != result) {
            LOG_ERR("CAN shutdown GPIO config failed: %d", result);
        }
    }

    if ((0 == result) && cfg->has_can_silent) {
        result = gpio_pin_configure_dt(&cfg->can_silent, GPIO_OUTPUT_INACTIVE);
        if (0 != result) {
            LOG_ERR("CAN silent GPIO config failed: %d", result);
        }
    }

    /* Configure bus select mux GPIOs if present (Rev2 only) */
    if ((0 == result) && cfg->has_bus_select) {
        result = gpio_pin_configure_dt(&cfg->bus_sel[0], GPIO_OUTPUT_INACTIVE);
        if (0 == result) {
            result = gpio_pin_configure_dt(&cfg->bus_sel[1], GPIO_OUTPUT_INACTIVE);
        }
    }

    return result;
}

/**
 * @brief Zephyr driver init: configure ADC, CAN GPIOs, and optional bus-select mux.
 *
 * Called by the kernel at POST_KERNEL priority 91. ADC init failure is non-fatal
 * (voltage reads return -1 but GPIO operations still work). GPIO init failures
 * are fatal and propagate the error code back to the kernel.
 *
 * @param dev Power subsystem device handle.
 * @return 0 on success, negative errno if a GPIO could not be configured.
 */
static Status_t power_init(const struct device *dev)
{
    const struct power_config *cfg = dev->config;
    struct power_data *data = dev->data;
    Status_t result = 0;

#if defined(CONFIG_SOC_FAMILY_STM32)
    /* Release any GPIO pulls latched by a previous power_shutdown(). Must run
     * before the CAN control pins are reconfigured below so a warm start comes
     * up in the same state as a cold boot. */
    clear_standby_pull_config();
#endif

    /* Verify the VBUS regulator device is ready */
    if (!device_is_ready(cfg->vbus_reg)) {
        LOG_ERR("VBUS regulator device not ready");
        result = -ENODEV;
    } else {
        /* Non-fatal if ADC init fails — GPIO operations (VBUS, mux, CAN)
         * still work, only voltage reads return -1. This allows the driver
         * to function on native_sim where the ADC emulator has limited
         * reference support. */
        setup_battery_adc(cfg, data);

        result = configure_can_gpios(cfg);

        /* Sanity check the optional VCC sense sensor (e.g. st,stm32-vbat).
         * Non-fatal if absent or not ready — VCC reads return -1.0 via
         * the has_vcc_sense gate in sample_vcc_voltage. */
        if ((0 == result) && cfg->has_vcc_sense &&
            (false == device_is_ready(cfg->vcc_sense_dev))) {
            LOG_WRN("VCC sense sensor not ready (VCC reads disabled)");
        }

        if (0 == result) {
            const char *vcc_state = "absent";
            if (cfg->has_vcc_sense && (true == device_is_ready(cfg->vcc_sense_dev))) {
                vcc_state = "ready";
            }
            LOG_INF("Power subsystem initialized (batt-divider=%u.%02ux, vcc-sense=%s)",
                cfg->battery_divider_ratio / BATTERY_DIVIDER_WHOLE_SCALE,
                (cfg->battery_divider_ratio % BATTERY_DIVIDER_WHOLE_SCALE) / BATTERY_DIVIDER_FRACTION_SCALE,
                vcc_state);
        }
    }

    return result;
}

/* ---- Device instantiation ---- */

#define POWER_HAS_PROP(inst, prop) DT_INST_NODE_HAS_PROP(inst, prop)
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
